DF4IAH/HFT-Core-Module/CAD/Eagle/HFT-Core-Module_1V0_BOM.txt

Stückliste exportiert aus /Users/espero/nfs_ds_nfs/git/HFT-Core-Module__HW_1V0/CAD/Eagle/HFT-Core-Module_1V0.sch am 10.08.18 23:08

Qty Value                                             Device                             Package                            Parts                                                                                                                                                                                                                                                                                                                                                                                                                                                                                                                                                                                                      Description                                                 
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
84  47R                                               R-EU_R0603                         R0603                              R0241, R0242, R0243, R0251, R0252, R0253, R0254, R0261, R0262, R0263, R0269, R0271, R0272, R0273, R0274, R0275, R0276, R0277, R0281, R0282, R0283, R0284, R0285, R0286, R0287, R0288, R0289, R0290, R0291, R0292, R0293, R0294, R0295, R0296, R0642, R0713, R0714, R0723, R0724, R0731, R0732, R0735, R0736, R0743, R0744, R0802, R0803, R0831, R1021, R1041, R1051, R1061, R1106, R1107, R1108, R1109, R1114, R2310, R2311, R2312, R2313, R2314, R2315, R2316, R2317, R2318, R2320, R2321, R2322, R2323, R2324, R2325, R2326, R2327, R2328, R2330, R2331, R2332, R2333, R2334, R2335, R2336, R2337, R2338 RESISTOR, European symbol                                   
7   47pF                                              C-EUC0603                          C0603                              C0844, C0846, C0851, C0852, C0873, C0875, C1113                                                                                                                                                                                                                                                                                                                                                                                                                                                                                                                                                            CAPACITOR, European symbol                                  
3   47uF                                              C-EUC0805                          C0805                              C1406, C1602, C1606                                                                                                                                                                                                                                                                                                                                                                                                                                                                                                                                                                                        CAPACITOR, European symbol                                  
1   5.2kR                                             R-EU_R0603                         R0603                              R1202                                                                                                                                                                                                                                                                                                                                                                                                                                                                                                                                                                                                      RESISTOR, European symbol                                   
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
