DF4IAH/HFT-Core-Module/CAD/Eagle/Extensions/Manufacturing/Pictures/HFT-ArduinoShield-Module_1V0__BottomCopper.png

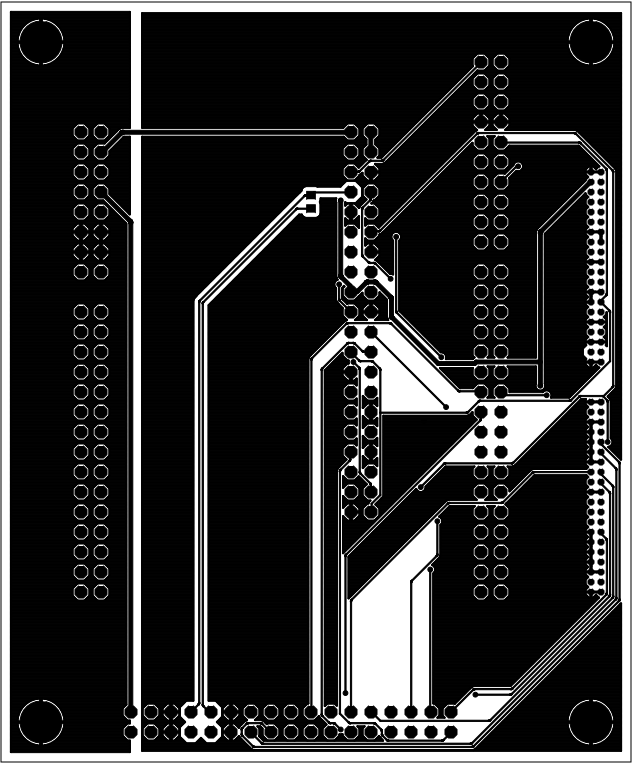
CAD/Eagle/Extensions/Manufacturing/Pictures/HFT-ArduinoShield-Module_1V0__BottomCopper.png
