DF4IAH/HFT-Core-Module/CAD/Eagle/Extensions/Manufacturing/Pictures/HFT-ArduinoShield-Module_1V0__Top.png

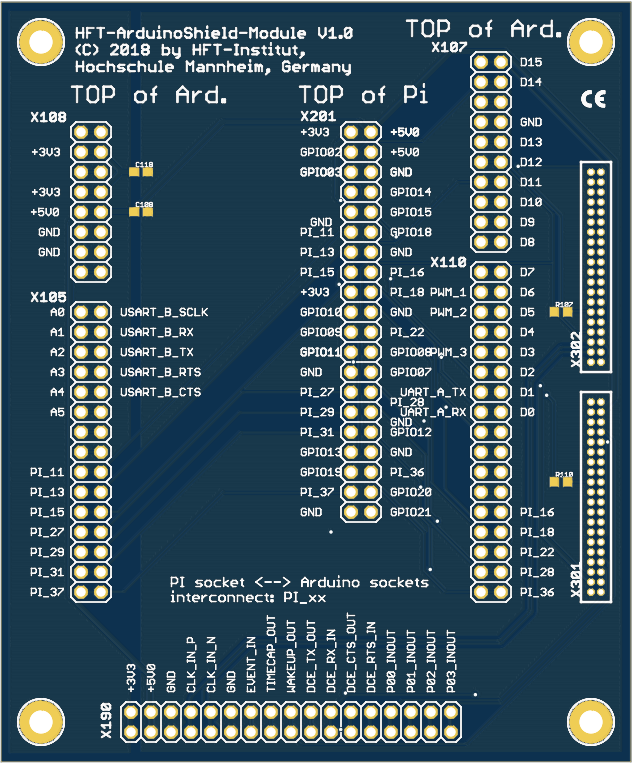
CAD/Eagle/Extensions/Manufacturing/Pictures/HFT-ArduinoShield-Module_1V0__Top.png
