DF4IAH/HFT-Core-Module/CAD/Eagle/Extensions/Manufacturing/Pictures/HFT-ArduinoShield-Module_1V0__TopSilkscreen.png

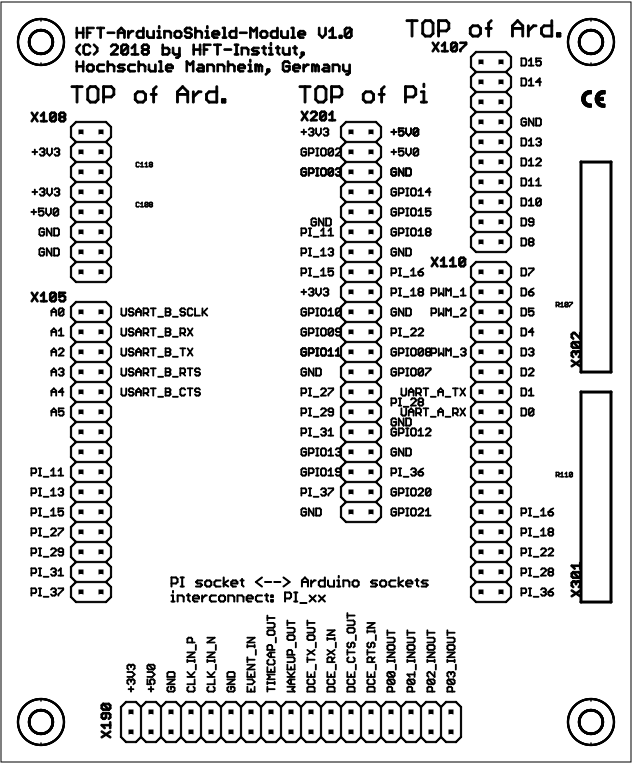
CAD/Eagle/Extensions/Manufacturing/Pictures/HFT-ArduinoShield-Module_1V0__TopSilkscreen.png
