DF4IAH/HFT-Core-Module/CAD/Eagle/Extensions/Manufacturing/Pictures/HFT-ArduinoShield-Module_1V0__TopSoldermask.png

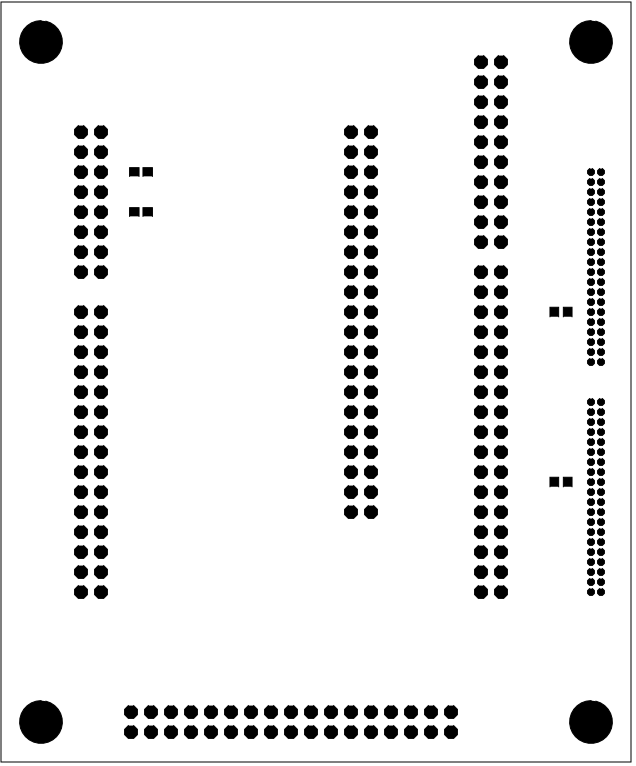
CAD/Eagle/Extensions/Manufacturing/Pictures/HFT-ArduinoShield-Module_1V0__TopSoldermask.png
