DF4IAH/HFT-Core-Module/CAD/Eagle/Manufacturing/Pictures/HFT-Core-Module_1V0__Bottom.png

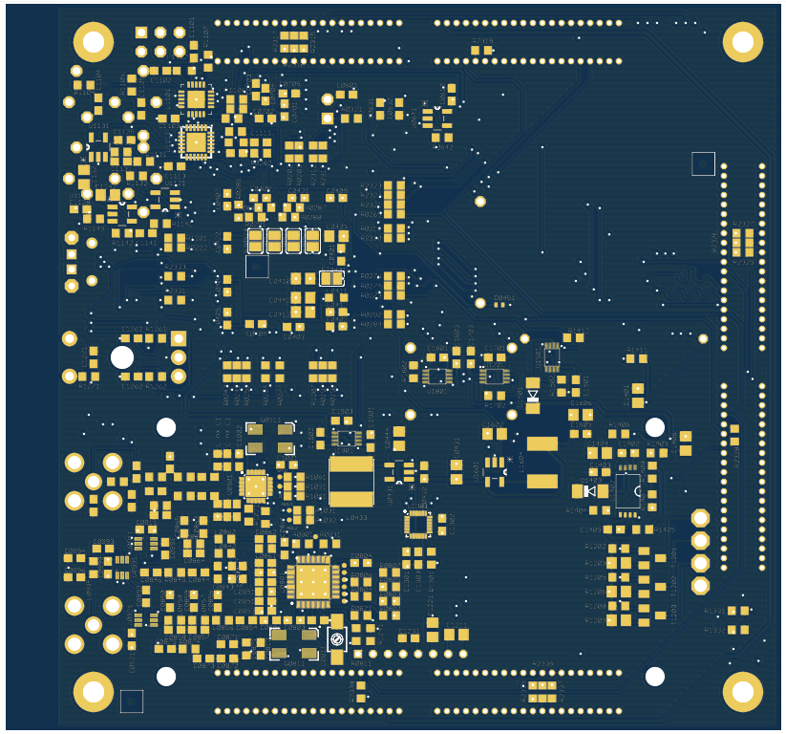
CAD/Eagle/Manufacturing/Pictures/HFT-Core-Module_1V0__Bottom.png
