DF4IAH/HFT-Core-Module/Docs/09_Results/Pictures/1V0_4-Layers_Dirty-PCB/PCB-package_1V0__IMG_2087.JPG

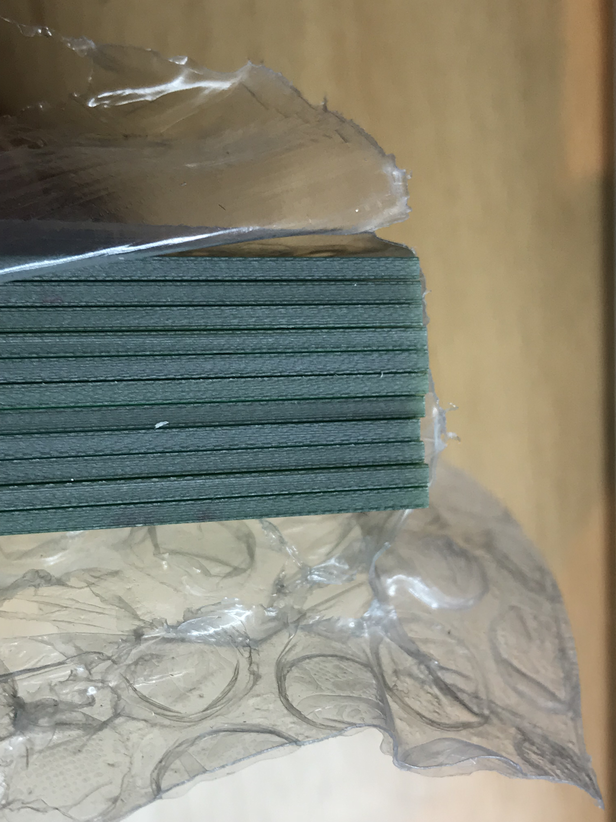
Docs/09_Results/Pictures/1V0_4-Layers_Dirty-PCB/PCB-package_1V0__IMG_2087.JPG
