DF4IAH/HFT-Core-Module/Docs/09_Results/Pictures/1V1_6-Layers_Beta-Layout/1_Preview_TOP.png

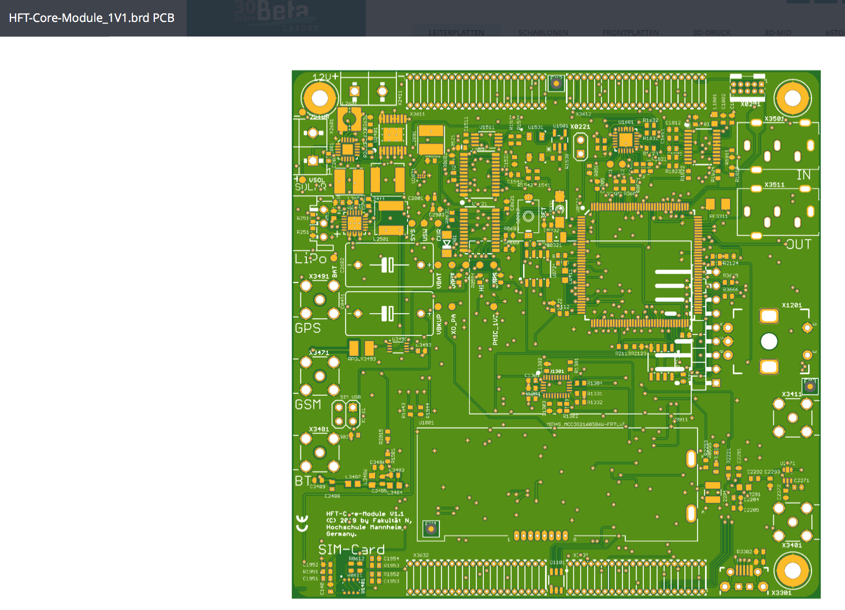
Docs/09_Results/Pictures/1V1_6-Layers_Beta-Layout/1_Preview_TOP.png
