DF4IAH/HFT-Core-Module/Docs/09_Results/Pictures/1V1_6-Layers_Beta-Layout/6_FITS-or-NOT.png

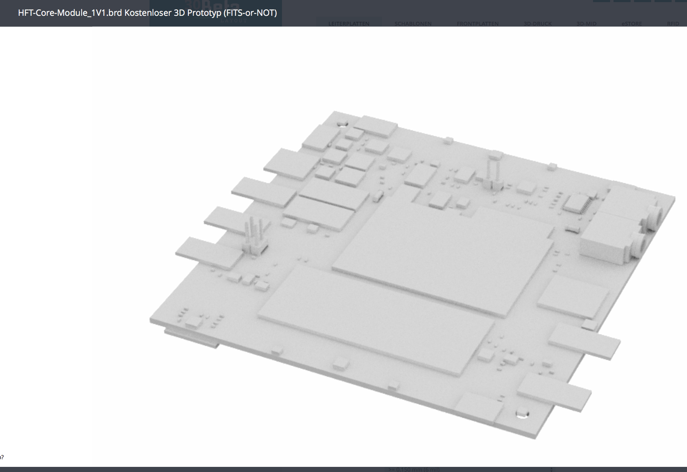
Docs/09_Results/Pictures/1V1_6-Layers_Beta-Layout/6_FITS-or-NOT.png
