DF4IAH/HFT-Core-Module/SW/HFT-Core-Module_TrueSTUDIO/App/Inc/task_Controller.h

/*
 * task_Controller.h
 *
 *  Created on: 11.09.2018
 *      Author: DF4IAH
 */

#ifndef TASK_CONTROLLER_H_
#define TASK_CONTROLLER_H_

#include "stm32l4xx_hal.h"
#include "main.h"


#define CONTROLLER_MSG_Q_LEN                                  8


typedef enum ControllerMsgDestinations_ENUM {

  Destinations__Unspec                                        = 0,
  Destinations__Controller,
  Destinations__Main_Default,

  Destinations__Osc_TCXO,
  Destinations__Osc_Si5338,

  Destinations__Network_USBtoHost,
  Destinations__Network_USBfromHost,

  Destinations__Actor_LCD,

  Destinations__Sensor_Baro,
  Destinations__Sensor_Hygro,
  Destinations__Sensor_Gyro,

  Destinations__Radio_AX5243,
  Destinations__Radio_SX1276,

  Destinations__Audio_ADC,
  Destinations__Audio_DAC,

} ControllerMsgDestinations_t;


typedef struct ControllerMods {

  uint8_t                           rtos_Default;
  uint8_t                           network_USBtoHost;
  uint8_t                           network_USBfromHost;
  uint8_t                           osc_TCXO;
  uint8_t                           osc_Si5338;
  uint8_t                           actor_LCD;
  uint8_t                           sensor_Baro;
  uint8_t                           sensor_Hygro;
  uint8_t                           sensor_Gyro;
  uint8_t                           radio_AX5243;
  uint8_t                           radio_SX1276;
  uint8_t                           audio_ADC;
  uint8_t                           audio_DAC;

} ControllerMods_t;


typedef enum ControllerMsgControllerCmds_ENUM {

  MsgController__InitDo                                       = 0x01U,
  MsgController__InitDone,

  MsgController__DeInitDo                                     = 0x05U,

//MsgController__SetVar01                                     = 0x41U,

//MsgController__GetVar01                                     = 0x81U,

  MsgController__CallFunc01_CyclicTimerEvent                  = 0xc1U,
  MsgController__CallFunc02_CyclicTimerStart,
  MsgController__CallFunc03_CyclicTimerStop,

} ControllerMsgControllerCmds_t;


typedef struct ControllerMsg2Proc {

  uint32_t                            rawAry[CONTROLLER_MSG_Q_LEN];
  uint8_t                             rawLen;

  ControllerMsgDestinations_t         msgSrc;
  ControllerMsgDestinations_t         msgDst;                                                         // Not in use yet
  ControllerMsgControllerCmds_t       msgCmd;
  uint8_t                             msgLen;

  uint8_t                             bRemain;

  uint8_t                             optLen;
  uint8_t                             optAry[CONTROLLER_MSG_Q_LEN << 2];

} ControllerMsg2Proc_t;



uint32_t controllerCalcMsgHdr(ControllerMsgDestinations_t dst, ControllerMsgDestinations_t src, uint8_t lengthBytes, uint8_t cmd);

uint32_t controllerMsgPushToInQueue(uint8_t msgLen, uint32_t* msgAry, uint32_t waitMs);
void controllerMsgPushToOutQueue(uint8_t msgLen, uint32_t* msgAry, uint32_t waitMs);
uint32_t controllerMsgPullFromOutQueue(uint32_t* msgAry, ControllerMsgDestinations_t dst, uint32_t waitMs);

void controllerTimerCallback(void const *argument);


/* Task */

void controllerTaskInit(void);
void controllerTaskLoop(void);

#endif /* TASK_CONTROLLER_H_ */
