DF4IAH/HFT-Core-Module/SW/HFT-Core-Module_TrueSTUDIO/App/Src/task_AX5243.c

/*
 * task_AX5243.c
 *
 *  Created on: 10.09.2018
 *      Author: DF4IAH
 */


/* Includes ------------------------------------------------------------------*/
#include <string.h>
#include <ctype.h>
#include <task_USB.h>
#include "FreeRTOS.h"
#include "cmsis_os.h"
#include "stm32l496xx.h"
//#include "stm32l4xx_hal_def.h"
//#include "stm32l4xx_hal_gpio.h"

#include "bus_spi.h"
#include "task_Controller.h"

#include "task_AX5243.h"


extern osSemaphoreId        c2Ax5243_BSemHandle;
extern osSemaphoreId        spi3_BSemHandle;
extern osSemaphoreId        usbToHost_BSemHandle;

extern EventGroupHandle_t   extiEventGroupHandle;
extern EventGroupHandle_t   spiEventGroupHandle;
extern EventGroupHandle_t   globalEventGroupHandle;

extern ENABLE_MASK_t        g_enableMsk;
extern MON_MASK_t           g_monMsk;

extern SPI_HandleTypeDef    hspi3;
extern DMA_HandleTypeDef    hdma_spi3_rx;
extern DMA_HandleTypeDef    hdma_spi3_tx;

extern uint8_t              spi3TxBuffer[SPI3_BUFFERSIZE];
extern uint8_t              spi3RxBuffer[SPI3_BUFFERSIZE];


/* BLOCK of DEFINITIONS */

//# define  AX_RUN_VCO2_APRS_TX       1U

//# define  AX_TEST_VCO1_BANDENDS     1U
//# define  AX_TEST_VCO1_FSK_TX       1U
//# define  AX_TEST_VCO1_FSK_RX       1U
//# define  AX_TEST_VCO1_POCSAG_TX    1U
//# define  AX_TEST_VCO1_POCSAG_RX    1U

//# define  AX_TEST_VCO2_BANDENDS     1U
//# define  AX_TEST_VCO2_ANALOG_FM_TX 1U
//# define  AX_TEST_VCO2_ANALOG_FM_RX 1U
//# define  AX_TEST_VCO2_PR1200_TX    1U
//# define  AX_TEST_VCO2_PR1200_RX    1U


#if defined(AX_TEST_VCO1_BANDENDS) | defined(AX_TEST_VCO1_FSK_TX)   | defined(AX_TEST_VCO1_FSK_RX)      | defined(AX_TEST_VCO1_FSK_RX)    | defined(AX_TEST_VCO1_POCSAG_RX) | \
  defined(AX_TEST_VCO2_BANDENDS) | defined(AX_TEST_VCO2_ANALOG_FM_TX) | defined(AX_TEST_VCO2_ANALOG_FM_RX)  | defined(AX_TEST_VCO2_PR1200_TX) | defined(AX_TEST_VCO2_PR1200_RX)
# ifndef AX_TEST
# define AX_TEST 1U
# endif
#endif


static const uint16_t       c_ax_pwr_ary[C_AX_PRW_LENGTH]     = {
  // -10.4  (< -20dBm)
  0x0000UL,

  // -10.2  (-20dBm)
  0x000aUL,

  // -10.0 .. - 9.1
    170,    173,    175,    178,    180,    182,    184,    186,    188,    189,

  // - 9.0 .. - 8.1
    191,    193,    194,    196,    198,    199,    201,    203,    205,    207,

  // - 8.0 .. - 7.1
    209,    211,    214,    216,    219,    221,    224,    227,    230,    233,

  // - 7.0 .. - 6.1
    236,    239,    243,    246,    250,    253,    257,    260,    264,    267,

  // - 6.0 .. - 5.1
    271,    275,    278,    282,    285,    289,    292,    296,    299,    303,

  // - 5.0 .. - 4.1
    306,    309,    313,    317,    320,    324,    327,    331,    335,    338,

  // - 4.0 .. - 3.1
    342,    346,    350,    354,    358,    362,    366,    370,    374,    379,

  // - 3.0 .. - 2.1
    383,    387,    392,    397,    401,    406,    411,    416,    421,    426,

  // - 2.0 .. - 1.1
    431,    436,    441,    447,    452,    457,    462,    467,    471,    476,

  // - 1.0 .. - 0.1
    480,    484,    488,    492,    495,    499,    502,    506,    510,    514,

  //   0.0 .. + 0.9
    519,    524,    529,    535,    540,    547,    553,    559,    566,    573,

  // + 1.0 .. + 1.9
    580,    587,    594,    602,    609,    616,    624,    632,    640,    648,

  // + 2.0 .. + 2.1
    656,    664,    673,    681,    690,    699,    708,    718,    727,    737,

  // + 3.0 .. + 3.9
    747,    757,    768,    778,    789,    800,    812,    824,    836,    849,

  // + 4.0 .. + 4.9
    862,    876,    889,    903,    917,    930,    942,    954,    965,    974,

  // + 5.0 .. + 5.9
    982,    988,    993,    997,   1001,   1004,   1008,   1012,   1016,   1022,

  // + 6.0 .. + 6.9
   1030,   1039,   1051,   1064,   1078,   1095,   1112,   1131,   1151,   1171,

  // + 7.0 .. + 7.9
   1193,   1215,   1238,   1261,   1284,   1307,   1329,   1350,   1369,   1388,

  // + 8.0 .. + 8.9
   1404,   1419,   1431,   1443,   1454,   1466,   1477,   1489,   1503,   1518,

  // + 9.0 .. + 9.9
   1536,   1556,   1579,   1604,   1630,   1657,   1685,   1712,   1740,   1766,

  // +10.0 .. +10.9
   1792,   1816,   1839,   1861,   1884,   1907,   1931,   1956,   1984,   2014,

  // +11.0 .. +11.9
   2048,   2085,   2126,   2169,   2215,   2263,   2313,   2363,   2414,   2465,

  // +12.0 .. +12.9
   2516,   2566,   2616,   2666,   2717,   2770,   2824,   2881,   2941,   3004,

  // +13.0 .. +13.9
   3072,   3144,   3220,   3298,   3378,   3459,   3540,   3619,   3696,   3770,

  // +14.0 .. +14.9
   3840,   3905,   3963,   4015,   4058,   4093,   4095,   4095,   4095,   4095,

  // +15.0
   4095
};

#if 0
static const uint8_t        c_ax_pocsag_activation_code[][3]  = {
  { 0, 7, 0x32},
  { 0, 7, 0x22},
  { 0, 7, 0x35},
  { 0, 7, 0x33},
  { 0, 7, 0x33},
  { 0, 7, 0x34},
  { 0, 7, 0x34},
  { 0, 7, 0x34}
};
static const uint8_t        c_ax_pocsag_activation_code_len = sizeof(c_ax_pocsag_activation_code) / 3;
#endif

static uint8_t              s_ax5243_enable;                                                          // FLASH
static uint32_t             s_ax5243StartTime;
static uint8_t              s_ax_version;
static uint8_t              s_ax_aprs_enable;                                                         // FLASH
static uint8_t              s_ax_pocsag_enable;                                                       // FLASH
//static uint8_t            s_ax_pocsag_beacon_secs;                                                  // FLASH
//static AX_SET_TX_RX_MODE_t  s_ax_set_tx_rx_mode;
static AX_SET_MON_MODE_t    s_ax_set_mon_mode;                                                        // FLASH
//static struct spi_device  s_ax_spi_device_conf;
//static  uint8_t           s_ax_spi_packet_buffer[C_SPI_AX_BUFFER_LENGTH];
//static  uint8_t           s_ax_spi_rx_buffer[C_SPI_AX_BUFFER_LENGTH];
//static  uint16_t          s_ax_spi_rx_buffer_idx;
//static  uint8_t           s_ax_spi_rx_fifo_doService;
static  uint32_t            s_ax_spi_freq_chan[2];
static  uint8_t             s_ax_spi_range_chan[2];
//static  uint8_t           s_ax_spi_vcoi_chan[2];
//static  int8_t            s_ax_spi_rx_bgnd_rssi;
static  AX_RX_FIFO_MEAS_t   s_ax_rx_fifo_meas;

//static uint8_t            s_ax_pocsag_chime_enable;
static uint32_t             s_ax_pocsag_individual_ric;
//static uint8_t            s_ax_pocsag_news_idx;



/* Forward declarations */
static uint16_t spi_ax_pocsag_skyper_RubricString_Decode(char* outBuf, uint16_t outBufSize, const char* pocsagSkyperRubricMsg, uint16_t pocsagSkyperRubricMsgLen);
static uint16_t spi_ax_pocsag_skyper_NewsString_Decode(char* outBuf, uint16_t outBufSize, const char* pocsagSkyperNewsMsg, uint16_t pocsagSkyperNewsMsgLen);
static uint8_t spiDetectAX5243(void);

#ifdef AX_TEST
static void spi_test_start_testBox(void);
static void spi_ax_test_PR1200_Rx(void);
#endif


static uint8_t getCurrent_POCSAG_TimeSlot(void)
{
  /* Get up-to-date global data */
  const uint64_t l_seconds10 = getRunTimeCounterValue() / 100ULL;

  /* Each TimeSlot takes 6.4 secs */
  return (uint8_t) ((l_seconds10 >> 6) & 0x0f);
}

static void spi_ax_FIFO_CLEAR(void)
{
  /* FIFO do a CLEAR of data and flags */
  const uint8_t txMsg[2] = { 0x28U | C_AX_REG_WR,                                                     // WR address 0x28: FIFOCMD - AX_FIFO_CMD_CLEAR_FIFO_DATA_AND_FLAGS
      0x03U
  };
  spiProcessSpi3MsgTemplate(SPI3_AX, sizeof(txMsg), txMsg);
}

static void spi_ax_FIFO_COMMIT(void)
{
  /* FIFO do a COMMIT */
  const uint8_t txMsg[2] = { 0x28U | C_AX_REG_WR,                                                     // WR address 0x28: FIFOCMD - AX_FIFO_CMD_COMMIT
      0x04U
  };
  spiProcessSpi3MsgTemplate(SPI3_AX, sizeof(txMsg), txMsg);
}


#if 0

/* ISR routines */

/* PORTC Pin3 - AX5243 IRQ */
ISR(PORTC_INT0_vect, ISR_BLOCK)
{
  uint8_t processed = 0U;

  /* IRQREQUEST: check which request is on */
  spi_ax_transport(0U, "< 0c R2 >");                                                                  // RD address 0x0C: IRQREQUEST
  uint16_t ax_spi_irq_request = (uint16_t)g_ax_spi_packet_buffer[0] << 8 | g_ax_spi_packet_buffer[1];

  /* Reason(s) for interrupt */

  /* IRQRQFIFONOTEMPTY */
  if (ax_spi_irq_request & _BV(0)) {
    uint8_t fifoRssiCmd[2] = { 0x32 };                                                                // Own variant of RSSI FIFO message

    /* Get RSSI */
    spi_ax_transport(0U, "< 40 R1 >");                                                                // RD Address 0x40: RSSI
    fifoRssiCmd[1] = g_ax_spi_packet_buffer[0];

    /* Get local adjusted copies */
    int16_t l_ax_spi_rx_rssi    = (int8_t) (fifoRssiCmd[1]);
    int16_t l_ax_spi_rx_bgnd_rssi = g_ax_spi_rx_bgnd_rssi;

    /* 64 dB offset correction */
    l_ax_spi_rx_rssi    -= 64;
    l_ax_spi_rx_bgnd_rssi -= 64;

    /* Decrease background RSSI each time to avoid blocking */
    if (-170 < l_ax_spi_rx_bgnd_rssi) {
      --g_ax_spi_rx_bgnd_rssi;
    }

    /* Abort packet when signal strength indicator falls near background noise and at least some WORDS were detected */
    if ((g_ax_spi_rx_buffer_idx >= 0x10) && (l_ax_spi_rx_rssi < (l_ax_spi_rx_bgnd_rssi + 12))) {
      /* FRMMODE abort frame */
      spi_ax_transport(0U, "< 92 07 >");                                                              // WR address 0x12: FRAMING - CRCMODE: none, FRMMODE: Raw, Pattern Match 0x06, FABORT
    }

    /* Concatenate FIFO message to local buffer */
    isr_spi_ax_fifo_readMessage();

    /* Concatenate RSSI to local buffer */
    memcpy(g_ax_spi_rx_buffer + g_ax_spi_rx_buffer_idx, fifoRssiCmd, 2);
    g_ax_spi_rx_buffer_idx += 2;

    /* Inform front-end to process the data */
    g_ax_spi_rx_fifo_doService = 1U;
    processed = 1U;
  }

  /* IRQRFIFOERROR */
  if (ax_spi_irq_request & _BV(4)) {
    /* FIFOCMD / FIFOSTAT */
    spi_ax_FIFO_CLEAR();

    processed = 1U;
  }

  /* IRQRQPLLUNLOCK */
  if (ax_spi_irq_request & _BV(5)) {
    processed = 1U;
  }

  /* RADIO EVENT = REVMDONE */
  if (ax_spi_irq_request & _BV(6)) {
    const uint8_t fifoDoneCmd = 0x01;
    memcpy(g_ax_spi_rx_buffer + g_ax_spi_rx_buffer_idx, &fifoDoneCmd, 1);
    g_ax_spi_rx_buffer_idx++;

    /* Inform front-end to process the data */
    g_ax_spi_rx_fifo_doService = 1U;
    processed = 1U;
  }

  if (!processed) {
    /* unknown request */
  }
}

void spi_ax_ISR_setFlags(uint8_t flags)
{
  if (!flags) {
    irqflags_t flags = cpu_irq_save();

    /* Disable AX5243 interrupts */
    {
      /* FIFOCMD / FIFOSTAT */
      spi_ax_FIFO_CLEAR();

      /* IRQMASK: set to none */
      spi_ax_transport(0U, "< 86 00 00 >");                                                           // WR address 0x06: IRQMASK - clear all flags
    }

    /* Turn off MCU PORTC interrupts */
    PORTC_INTCTRL = PORT_INT1LVL_OFF_gc | PORT_INT0LVL_OFF_gc;

    cpu_irq_restore(flags);

  } else {
    /* PORTC Pin3 --> INT0 */
    irqflags_t flags = cpu_irq_save();

    /* PORTC Pin3 INPUT */
    ioport_set_pin_dir(AX_IRQ_PIN, IOPORT_DIR_INPUT);

    /* PORTC Pin3 PULLHIGH, Level: low active */
    ioport_set_pin_mode(AX_IRQ_PIN, IOPORT_MODE_PULLUP | IOPORT_MODE_INVERT_PIN);

    /* Interrupt priority levels for INT1 and INT0 = Low */
    PORTC_INTCTRL = PORT_INT1LVL_OFF_gc | PORT_INT0LVL_LO_gc;

    /* Map PORTC Pin3 --> INT0 */
    PORTC_INT0MASK = _BV(3);
    PORTC_INT1MASK = 0;

    /* Enable AX5243 interrupts */
    {
      /* FIFOCMD / FIFOSTAT */
      spi_ax_FIFO_CLEAR();

      /* PINFUNCIRQ */
      spi_ax_transport(0U, "< a4 43 >");                                                              // WR address 0x24: PINFUNCIRQ - set to IRQ source, no PULLUP = !0x80, inverse = 0x40

      /* RADIOEVENTMASK */
      spi_ax_transport(0U, "< 88 00 01 >");                                                           // WR address 0x08: RADIOEVENTMASK - set to not REVMRXPARAMSETCHG !0x08, not REVMRADIOSTATECHG !0x04, REVMDONE 0x01

      /* IRQMASK */
      spi_ax_transport(0U, "< 86 00 51 >");                                                           // WR address 0x06: IRQMASK - set to Bit06:IRQMRADIOCTRL 0x040, !Bit05:IRQRQPLLUNLOCK !0x020, Bit04:IRQMFIFOERROR 0x010, Bit0:IRQMFIFONOTEMPTY 0x001
    }

    /* Clear any pending INT1 / INT0 interrupts */
    PORTC_INTFLAGS = 0b00000011;

    /* Activation of all interrupts, again */
    cpu_irq_restore(flags);
  }
}

void isr_spi_ax_fifo_readMessage(void)
{
  /* Read the length of the message within the FIFO */
  spi_ax_transport(0U, "< 2a R2 >");                           // RD address 0x2A: FIFOCOUNT
  uint16_t msgLen = (uint16_t)g_ax_spi_packet_buffer[0] << 8 | g_ax_spi_packet_buffer[1];
  if ((g_ax_spi_rx_buffer_idx + msgLen) > 256) {
    msgLen = 256 - g_ax_spi_rx_buffer_idx;
  }

  /* Fetch the AX5243 FIFO content */
  uint8_t fifoDataAddr = 0x29;
  spi_select_device(&SPI_AX, &g_ax_spi_device_conf);
  spi_write_packet(&SPI_AX, &fifoDataAddr, 1);
  spi_read_packet(&SPI_AX, g_ax_spi_rx_buffer + g_ax_spi_rx_buffer_idx, msgLen);
  spi_deselect_device(&SPI_AX, &g_ax_spi_device_conf);

  g_ax_spi_rx_buffer_idx += msgLen;
}
#endif

#if 0
static uint8_t strGetHex(const char* str)
{
  unsigned int ret = 0;

  sscanf(str, "%02x", &ret);
  return (uint8_t)ret;
}

static uint8_t strGetDec(const char* str, int* o_val)
{
  return (uint8_t) sscanf(str, "%d", o_val);
}
#endif


#ifdef WHEN_NEEDED
static AX_POCSAG_CW2_t ax_pocsag_analyze_msg_tgtFunc_get(const char* msg, uint16_t msgLen)
{
  if (!msg || !msgLen) {
    return AX_POCSAG_CW2_MODE1_TONE;
  }

  for (uint16_t idx = 0; idx < msgLen; idx++) {
    char c = *(msg + idx);

    if (('0' <= c) && (c <= '9')) {
      continue;
    }

    if ((c == ' ') || (c == '-') || (toupper(c) == 'U') || (c == '[') || (c == ']') || (c == '(') || (c == ')')) {
      continue;
    }

    return AX_POCSAG_CW2_MODE3_ALPHANUM;
  }

  return AX_POCSAG_CW2_MODE0_NUMERIC;
}
#endif

static uint8_t spi_ax_pocsag_calc_evenParity(uint32_t par)
{
  par ^= par >> 0x01;
  par ^= par >> 0x02;
  par ^= par >> 0x04;
  par ^= par >> 0x08;
  par ^= par >> 0x10;
  par &= 1;

  return (uint8_t) par;
}

static uint32_t spi_ax_pocsag_calc_checkAndParity(uint32_t codeword_in)
{
  const uint32_t inPoly   = 0xfffff800UL & codeword_in;
  const uint32_t genPoly  = 0x769UL;                                                                  // Generating polynomial   x10 + x9 + x8 + x6 + x5 + x3 + 1
  uint32_t cw_calc        = inPoly;

  // Calculate the BCH check
  for (uint8_t idx = 31; idx >= 11; idx--) {
    if (cw_calc  & (1UL <<  idx)) {
      volatile uint32_t genPolyShifted = genPoly << (idx - 10);
      cw_calc ^= genPolyShifted;
      (void)genPolyShifted;
    }
  }
  cw_calc &= 0x000007feUL;

  /* Data with BCH check */
  cw_calc |= inPoly;

  /* Calculate for Even Parity */
  uint8_t par = spi_ax_pocsag_calc_evenParity(cw_calc);

  /* Data with 31:21 BCH and Parity */
  cw_calc |= par;

  return cw_calc;
}

static uint8_t spi_ax_pocsag_getBcd(char c)
{
  uint8_t u8;

  switch (c) {
    case 0x30:
    case 0x31:
    case 0x32:
    case 0x33:
    case 0x34:
    case 0x35:
    case 0x36:
    case 0x37:
    case 0x38:
    case 0x39:
      u8 = c - 0x30;
      break;

    case 0x23:                                                                                        // #
    case 0x2a:                                                                                        // *
      u8 = 0xa;
      break;

    case 0x55:                                                                                        // U
    case 0x75:                                                                                        // u
      u8 = 0xb;
      break;

    case 0x20:                                                                                        // ' '
      u8 = 0xc;
      break;

    case 0x2d:                                                                                        // -
      u8 = 0xd;
      break;

    case 0x5d:                                                                                        // ]
    case 0x29:                                                                                        // )
      u8 = 0xe;
      break;

    case 0x5b:                                                                                        // [
    case 0x28:                                                                                        // (
      u8 = 0xf;
      break;

    default:
      u8 = 0xc;                                                                                       // ' '
  }
  return u8;
}

static char spi_ax_pocsag_getReversedNumChar(uint8_t nibble)
{
  char c;

  switch (nibble) {
    case 0b0000:
      c = 0x30;
      break;

    case 0b1000:
      c = 0x31;
      break;

    case 0b0100:
      c = 0x32;
      break;

    case 0b1100:
      c = 0x33;
      break;

    case 0b0010:
      c = 0x34;
      break;

    case 0b1010:
      c = 0x35;
      break;

    case 0b0110:
      c = 0x36;
      break;

    case 0b1110:
      c = 0x37;
      break;

    case 0b0001:
      c = 0x38;
      break;

    case 0b1001:
      c = 0x39;
      break;

    case 0b0101:                                                                                      // #
      c = 0x23;
      break;

    case 0b1101:                                                                                      // U
      c = 0x55;
      break;

    case 0b0011:                                                                                      // ' '
      c = 0x20;
      break;

    case 0b1011:                                                                                      // -
      c = 0x2d;
      break;

    case 0b0111:                                                                                      // ]
      c = 0x5d;
      break;

    case 0b1111:                                                                                      // [
      c = 0x5b;
      break;

    default:
      c = 0x20;                                                                                       // ' '
  }
  return c;
}

static char spi_ax_pocsag_getReversedAlphaChar(uint8_t reversedIn)
{
  char c = 0;

  /* Reverse 7-bit to get ASCII */
  for (uint8_t idx = 0; idx < 7; idx++) {
    /* Take LSB */
    uint8_t bit = reversedIn & 0x01;

    /* Move bit to reversed target */
    c <<= 1;
    c  |= bit;
    reversedIn >>= 1;
  }
  return c;
}

static uint32_t spi_ax_pocsag_get20Bits(const char* tgtMsg, uint16_t tgtMsgLen, AX_POCSAG_CW2_t tgtFunc, uint16_t msgBitIdx)
{
  uint32_t msgWord = 0UL;
  uint16_t msgByteIdx;
  uint16_t msgByteIdxLast = 65535;
  uint8_t  byteBitPos;
  uint8_t  byte = 0;

  for (uint16_t bitCnt = 20; bitCnt; bitCnt--, msgBitIdx++) {
    if (tgtFunc == AX_POCSAG_CW2_MODE0_NUMERIC) {
      /* Calculate source byte and bit position of byte */
      msgByteIdx  = msgBitIdx >> 2;
      byteBitPos  = msgBitIdx & 0x3;

      /* Get the byte as NUMERIC - NUMERIC_SPACE when message exhausted */
      if (msgByteIdxLast != msgByteIdx) {
        msgByteIdxLast = msgByteIdx;
        byte = (msgByteIdx < tgtMsgLen) ?  spi_ax_pocsag_getBcd(*(tgtMsg + msgByteIdx)) : 0xc;
      }

    } else {
      /* Calculate source byte and bit position of byte */
      msgByteIdx  = msgBitIdx / 7;
      byteBitPos  = msgBitIdx % 7;

      /* Get the byte as ALPHA - NULL when message exhausted */
      if (msgByteIdxLast != msgByteIdx) {
        msgByteIdxLast = msgByteIdx;
        byte = (msgByteIdx < tgtMsgLen) ?  (uint8_t) *(tgtMsg + msgByteIdx) : 0;
      }
    }

    msgWord <<= 1;
    if (byte & (1U << byteBitPos)) {
      msgWord |= 0b1;
    }
  }
  return msgWord;
}

static char spi_ax_pocsag_getNumeric(const uint32_t* rcv20Bits, uint8_t rcv20BitsCnt, uint8_t msgNumIdx)
{
  uint8_t rcv20BitsIdx  = msgNumIdx / 5;
  uint8_t innerPos    = 4 - (msgNumIdx % 5);
  uint8_t mvCnt     = innerPos << 2;
  char numChar      = ' ';

  if (rcv20BitsIdx < rcv20BitsCnt) {
    /* Get nibble slice */
    uint8_t nibble = (*(rcv20Bits + rcv20BitsIdx) >> mvCnt) & 0x0f;
    numChar = spi_ax_pocsag_getReversedNumChar(nibble);
  }
  return numChar;
}

static char spi_ax_pocsag_getAlphanum(const uint32_t* rcv20Bits, uint8_t rcv20BitsCnt, uint8_t msgAlphaIdx)
{
  uint8_t   rcv20BitsStartWordPos = (msgAlphaIdx * 7) / 20;
  uint8_t   rcv20BitsStartBitPos  = (msgAlphaIdx * 7) - (rcv20BitsStartWordPos * 20);

  /* Check for overflow */
  if ((rcv20BitsStartBitPos > 13) && ((rcv20BitsStartWordPos + 1) >= rcv20BitsCnt)) {
    return ' ';
  }

  /* Preload with MSB 20 bits */
  uint32_t charHiPad = *(rcv20Bits + rcv20BitsStartWordPos);

  /* Decide whether word concatenation is needed */
  if (rcv20BitsStartBitPos <= 13) {
    /* No overlapping */
    charHiPad >>= (13 - rcv20BitsStartBitPos);

  } else {
    /* Complete with LSB part when overlapping */

    /* Load LSB part */
    uint32_t charLoPad = *(rcv20Bits + rcv20BitsStartWordPos + 1);

    /* Move upper part to right position */
    charHiPad <<= (rcv20BitsStartBitPos - 13);

    /* Move lower part to right position */
    charLoPad >>= (33 - rcv20BitsStartBitPos);

    /* Combine into MSB pad */
    charHiPad  |= charLoPad;
  }

  /* Get character of this 7-bit field */
  return spi_ax_pocsag_getReversedAlphaChar((uint8_t) (charHiPad & 0x0000007fUL));
}


static void spi_ax_pocsag_address_tone(uint8_t is_RIC_individual, uint32_t address, uint8_t fktBits)
{
  char isMyChar = is_RIC_individual ?  '*' : ' ';
  char isMyBeep = is_RIC_individual ?  0x07 : ' ';
  int  dbgLen;
  char dbgBuf[256];

  dbgLen = (uint8_t) sprintf(dbgBuf, "\r\n>>> TS=%1X %c Address=%8lu FktBits=0x%02x  (TONE   )%c%c%c\r\n", getCurrent_POCSAG_TimeSlot(), isMyChar, address, fktBits, isMyBeep, isMyBeep, isMyBeep);
  usbLogLen(dbgBuf, dbgLen);
}

static void spi_ax_pocsag_address_numeric(uint8_t is_RIC_individual, uint32_t address, uint8_t fktBits, uint32_t* dataAry, uint8_t dataCnt)
{
  char isMyChar = is_RIC_individual ?  '*' : ' ';
  char isMyBeep = is_RIC_individual ?  0x07 : ' ';
  uint8_t digitIdx = 0;
  int  dbgLen;
  char dbgBuf[256];

  dbgLen = (uint8_t) sprintf(dbgBuf, "\r\n>>> TS=%1X %c Address=%8lu FktBits=0x%02x  (NUMERIC):", getCurrent_POCSAG_TimeSlot(), isMyChar, address, fktBits);
  usbLogLen(dbgBuf, dbgLen);

  for (uint8_t dataCntIdx = 0; dataCntIdx < dataCnt; dataCntIdx++) {
    for (uint8_t sliceIdx = 0; sliceIdx < 5; sliceIdx++, digitIdx++) {
      dbgBuf[0] = spi_ax_pocsag_getNumeric(dataAry, dataCnt, digitIdx);
      usbLogLen(dbgBuf, 1);
    }
  }

  dbgLen = (uint8_t) sprintf(dbgBuf, "%c\r\n", isMyBeep);
  usbLogLen(dbgBuf, dbgLen);
}

static void spi_ax_pocsag_address_alphanum(uint8_t is_RIC_individual, uint32_t address, uint8_t fktBits, uint32_t* dataAry, uint8_t dataCnt, AX_POCSAG_IS_SKYPER_SPECIAL_t skyperSpecial)
{
  const char* typeStr = 0;
  char isMyChar = is_RIC_individual ?  '*' : ' ';
  char isMyBeep = is_RIC_individual ?  0x07 : ' ';
  int  dbgLen;
  char dbgBuf[256];
  char l_buf[256];

  switch (skyperSpecial) {
    case 1:
      typeStr = "RUBRIC ";
    break;

    case 2:
      typeStr = "NEWS   ";
    break;

    default:
      typeStr = "ALPHA  ";
  }

  dbgLen = (uint8_t) sprintf(dbgBuf, "\r\n>>> TS=%1X %c Address=%8lu FktBits=0x%02x  (%s):", getCurrent_POCSAG_TimeSlot(), isMyChar, address, fktBits, typeStr);
  usbLogLen(dbgBuf, dbgLen);
  dbgLen = 0;

  uint8_t alphaCnt = (dataCnt * 20) / 7;
  if (alphaCnt >= sizeof(dbgBuf)) {
    /* Buffer overflow */
    return;
  }

  /* Get text data */
  for (uint8_t alphaIdx = 0; alphaIdx < alphaCnt; alphaIdx++) {
    dbgBuf[dbgLen++] = spi_ax_pocsag_getAlphanum(dataAry, dataCnt, alphaIdx);
  }

  switch (skyperSpecial) {
    case 1:
      /* Decode Rubric content */
      dbgLen = spi_ax_pocsag_skyper_RubricString_Decode(l_buf, sizeof(l_buf), dbgBuf, dbgLen);
      usbLogLen(l_buf, dbgLen);
    break;

    case 2:
      /* Decode News content */
      dbgLen = spi_ax_pocsag_skyper_NewsString_Decode(l_buf, sizeof(l_buf), dbgBuf, dbgLen);
      usbLogLen(l_buf, dbgLen);
    break;

    default:
      usbLogLen(dbgBuf, dbgLen);
  }

  dbgLen = (uint8_t) sprintf(dbgBuf, "%c\r\n", isMyBeep);
  usbLogLen(dbgBuf, dbgLen);
}

static void spi_ax_pocsag_address_skyper_activation(uint8_t is_RIC_individual, uint32_t address, uint8_t fktBits, uint32_t* dataAry, uint8_t dataCnt)
{
  char isMyChar = is_RIC_individual ?  '*' : ' ';
  char isMyBeep = is_RIC_individual ?  0x07 : ' ';
  int  dbgLen;
  char dbgBuf[256];

  dbgLen = (uint8_t) sprintf(dbgBuf, "\r\n>>> TS=%1X %c Address=%8lu FktBits=0x%02x  (ACTIVTN):", getCurrent_POCSAG_TimeSlot(), isMyChar, address, fktBits);
  usbLogLen(dbgBuf, dbgLen);

  dbgLen = (uint8_t) sprintf(dbgBuf, " TODO! %c%c%c\r\n", isMyBeep, isMyBeep, isMyBeep);
  usbLogLen(dbgBuf, dbgLen);
}


#if 0
static uint16_t spi_ax_pocsag_skyper_RIC2ActivationString(char* outBuf, uint16_t outBufSize, uint32_t RIC)
{
  uint16_t outLen = 0;

  /* Sanity checks */
  if (!outBuf || outBufSize <= c_ax_pocsag_activation_code_len) {
    return 0;
  }

  for (uint16_t codeIdx = 0; codeIdx < c_ax_pocsag_activation_code_len; codeIdx++) {
    outBuf[outLen++] = (((RIC
              >> c_ax_pocsag_activation_code[codeIdx][AX_POCSAG_SKYPER_ACTIVATION_ARY_SHIFT])
              &  c_ax_pocsag_activation_code[codeIdx][AX_POCSAG_SKYPER_ACTIVATION_ARY_MASK])
              +  c_ax_pocsag_activation_code[codeIdx][AX_POCSAG_SKYPER_ACTIVATION_ARY_OFFSET])
              &  0x7f;                              // ASCII-7bit
  }
  outBuf[outLen] = 0;

  return outLen;
}
#endif

const char          PM_POCSAG_SKYPER_TIME[]         = "%02d%02d%02d   %02d%02d%02d";
#if 0
static uint16_t spi_ax_pocsag_skyper_TimeString(char* outBuf, uint16_t outBufSize, struct calendar_date* calDat)
{
  /* Sanity checks */
  if (!outBuf || outBufSize <= 15) {
    return 0;
  }

  /* Put calendar information into Skyper time message form */
  return (uint16_t) snprintf(outBuf, outBufSize, PM_POCSAG_SKYPER_TIME, calDat->hour, calDat->minute, calDat->second, calDat->date + 1, calDat->month + 1, calDat->year % 100);
}
#endif

#if 0
const char          PM_POCSAG_SKYPER_RUBRIC_ENC[]     = "1%c%c";
static uint16_t spi_ax_pocsag_skyper_RubricString_Encode(char* outBuf, uint16_t outBufSize, uint8_t rubricNumber, const char* rubricLabel, uint16_t rubricLabelLen)
{
  /* Sanity checks */
  if (!outBuf || outBufSize < 4) {
    return 0;
  }

  /* Put rubric label into Skyper rubric message form */
  uint16_t outLen = snprintf(outBuf, outBufSize, PM_POCSAG_SKYPER_RUBRIC_ENC, ' ' + (rubricNumber - 1), ' ' + 10);

  char* outBuf_ptr    = outBuf + outLen;
  const char* read_ptr  = rubricLabel;
  for (uint16_t idx = 0; idx < rubricLabelLen; idx++) {
    *(outBuf_ptr++) = *(read_ptr++) + 1;

    /* Target buffer runs out of space */
    if (++outLen >= (outBufSize - 1)) {
      break;
    }
  }
  *outBuf_ptr = 0;
  return outLen;
}
#endif

const char          PM_POCSAG_SKYPER_RUBRIC_DEC[]     = "Rubric=%02d, MaxEntries=%02d, Name: ";
static uint16_t spi_ax_pocsag_skyper_RubricString_Decode(char* outBuf, uint16_t outBufSize, const char* pocsagSkyperRubricMsg, uint16_t pocsagSkyperRubricMsgLen)
{
  /* Sanity checks */
  if (!outBuf || outBufSize < 8 || pocsagSkyperRubricMsgLen < 3) {
    return 0;
  }

  uint8_t rubricNumber  = (pocsagSkyperRubricMsg[1] - ' ') + 1;
  uint8_t rubricSize    = pocsagSkyperRubricMsg[2] - ' ';
  uint16_t outLen     = snprintf(outBuf, outBufSize, PM_POCSAG_SKYPER_RUBRIC_DEC, rubricNumber, rubricSize);

  char* outBuf_ptr    = outBuf + outLen;
  const char* read_ptr  = pocsagSkyperRubricMsg + 3;
  for (uint16_t idx = 3; idx < pocsagSkyperRubricMsgLen; idx++) {
    *(outBuf_ptr++) = *(read_ptr++) - 1;

    /* Target buffer runs out of space */
    if (++outLen >= (outBufSize - 1)) {
      break;
    }
  }
  *outBuf_ptr = 0;
  return outLen;
}

#if 0
const char          PM_POCSAG_SKYPER_NEWS_ENC[]       = "%c%c";
static uint16_t spi_ax_pocsag_skyper_NewsString_Encode(char* outBuf, uint16_t outBufSize, uint8_t rubricNumber, uint8_t newsNumber, const char* newsString, uint16_t newsStringLen)
{
  /* Sanity checks */
  if (!outBuf || outBufSize < 2) {
    return 0;
  }

  /* Put news into Skyper news message form */
  uint16_t outLen = snprintf(outBuf, outBufSize, PM_POCSAG_SKYPER_NEWS_ENC, ' ' + (rubricNumber - 1), ' ' + newsNumber);

  char* outBuf_ptr    = outBuf + outLen;
  const char* read_ptr  = newsString;
  for (uint16_t idx = 0; idx < newsStringLen; idx++) {
    *(outBuf_ptr++) = *(read_ptr++) + 1;

    /* Target buffer runs out of space */
    if (++outLen >= (outBufSize - 1)) {
      break;
    }
  }
  *outBuf_ptr = 0;
  return outLen;
}
#endif

const char          PM_POCSAG_SKYPER_NEWS_DEC[]       = "Rubric=%02d, News#=%02d, Text: ";
static uint16_t spi_ax_pocsag_skyper_NewsString_Decode(char* outBuf, uint16_t outBufSize, const char* pocsagSkyperNewsMsg, uint16_t pocsagSkyperNewsMsgLen)
{
  /* Sanity checks */
  if (!outBuf || outBufSize < 8 || pocsagSkyperNewsMsgLen < 2) {
    return 0;
  }

  uint8_t rubricNumber  = (pocsagSkyperNewsMsg[0] - ' ') + 1;
  uint8_t newsNumber    = pocsagSkyperNewsMsg[1] - ' ';
  uint16_t outLen     = snprintf(outBuf, outBufSize, PM_POCSAG_SKYPER_NEWS_DEC, rubricNumber, newsNumber);

  char* outBuf_ptr    = outBuf + outLen;
  const char* read_ptr  = pocsagSkyperNewsMsg + 2;
  for (uint16_t idx = 2; idx < pocsagSkyperNewsMsgLen; idx++) {
    *(outBuf_ptr++) = *(read_ptr++) - 1;

    /* Target buffer runs out of space */
    if (++outLen >= (outBufSize - 1)) {
      break;
    }
  }
  *outBuf_ptr = 0;
  return outLen;
}


static void spi_ax_pocsag_wordDecoder(AX_POCSAG_DECODER_DATA_t* l_pocsagData, uint32_t pocsagWord, uint8_t pocsagWordCnt)
{
  uint8_t tryBits = 32;

  /* Sanity check */
  if (!l_pocsagData) {
    return;
  }

  /* Preparations */
  l_pocsagData->badDecode     = 1U;                                                                   // No decoding data result
  l_pocsagData->badParity     = 1U;                                                                   // Parity check on non-modified data failed
  l_pocsagData->badCheck      = 1U;                                                                   // Check on non-modified data failed
  l_pocsagData->isAddr        = 0U;
  l_pocsagData->isData        = 0U;
  l_pocsagData->addrData      = 0UL;
  l_pocsagData->functionBits  = 0;

  /* Outer loop for one bit error corrections */
  do {
    l_pocsagData->invertedBit = tryBits;

    /* Try this pattern */
    uint32_t l_pocsagWord = pocsagWord;
    if ((0x00 <= tryBits) && (tryBits < 0x20)) {
      l_pocsagWord ^= (1UL << tryBits);
    }

    /* Inner loop for CODEWORD under test */
    do {
      /* Parity check */
      uint8_t  parCalc   = spi_ax_pocsag_calc_evenParity(l_pocsagWord & 0xfffffffe);
      uint8_t  parData   = (l_pocsagWord & 0x00000001) != 0;
      uint8_t  l_badParity = (parCalc != parData);
      if (tryBits == 0x20) {
        l_pocsagData->badParity = l_badParity;
      }
      if (l_badParity) {
        break;
      }

      /* Check calculation */
      uint32_t  chkCalc   = spi_ax_pocsag_calc_checkAndParity(l_pocsagWord);
      uint8_t    l_badCheck  = (chkCalc != l_pocsagWord);
      if (tryBits == 0x20) {
        l_pocsagData->badCheck = l_badCheck;

        if (l_badCheck && !l_badParity) {
          /* At least 2 bit errors detected - abort */
          return;
        }
      }
      if (l_badCheck) {
        break;
      }

      /* Address / Data assignment */
      l_pocsagData->badDecode = 0U;
      if (!(l_pocsagWord & 0x80000000UL)) {
        /* Address - HI-part concatenated by LO-part */
        l_pocsagData->isAddr  = 1U;
        l_pocsagData->addrData  = ((l_pocsagWord >> 10) & 0x001ffff8UL) | ((pocsagWordCnt >> 1) & 0b111);

        /* Function bits */
        l_pocsagData->functionBits = (uint8_t) ((l_pocsagWord >> 11) & 0b11);

      } else {
        /* Data */
        l_pocsagData->isData  = 1U;
        l_pocsagData->addrData  = ((l_pocsagWord >> 11) & 0x000fffffUL);
      }
      return;
    } while (0U);
  } while (tryBits--);
}

static void spi_ax_pocsag_messageDecoder(uint32_t address, uint8_t functionBits, uint32_t* dataAry, uint8_t dataCnt)
{
  uint8_t isSkyper = 1U;

  if (isSkyper) {
    uint32_t l_ax_pocsag_individual_ric = s_ax_pocsag_individual_ric;

    switch (address) {
      case AX_POCSAG_SKYPER_RIC_CLOCK:
      {
        if (functionBits == AX_POCSAG_CW2_MODE0_NUMERIC) {
          /* Time information */
          spi_ax_pocsag_address_numeric(0U, address, functionBits, dataAry, dataCnt);                 // TODO: DEBUGGING ONLY
        }
      }
      break;

      case AX_POCSAG_SKYPER_RIC_RUBRICS:
      {
        if (functionBits == AX_POCSAG_CW2_MODE3_ALPHANUM) {
          /* Store list of Rubrics */
          spi_ax_pocsag_address_alphanum(0U, address, functionBits, dataAry, dataCnt, AX_POCSAG_IS_SKYPER_SPECIAL_RUBRIC);   // TODO: DEBUGGING ONLY
        }
      }
      break;

      case AX_POCSAG_SKYPER_RIC_NEWS:
      {
        if (functionBits == AX_POCSAG_CW2_MODE3_ALPHANUM) {
          /* Store News into rubrics */
          spi_ax_pocsag_address_alphanum(0U, address, functionBits, dataAry, dataCnt, AX_POCSAG_IS_SKYPER_SPECIAL_NEWS);   // TODO: DEBUGGING ONLY
        }
      }
      break;

      case 0:
      {
        /* Drop non-valid address */
      }
      break;

      default:
      {
        uint8_t is_RIC_individual = address == l_ax_pocsag_individual_ric;
        switch (functionBits) {
          case AX_POCSAG_CW2_MODE2_ACTIVATION:
          {
            /* Check activation */
            spi_ax_pocsag_address_skyper_activation(is_RIC_individual, address, functionBits, dataAry, dataCnt);
          }
          break;

          case AX_POCSAG_CW2_MODE0_NUMERIC:
          {
            /* Numeric decoder */
            spi_ax_pocsag_address_numeric(is_RIC_individual, address, functionBits, dataAry, dataCnt);
          }
          break;

          case AX_POCSAG_CW2_MODE1_TONE:
          {
            /* Beep */
            spi_ax_pocsag_address_tone(is_RIC_individual, address, functionBits);
          }
          break;

          case AX_POCSAG_CW2_MODE3_ALPHANUM:
          {
            /* Alphanum decoder */
            spi_ax_pocsag_address_alphanum(is_RIC_individual, address, functionBits, dataAry, dataCnt, AX_POCSAG_IS_SKYPER_SPECIAL_NO);
          }
          break;
        }  // switch (functionBits)
      }
    }  // switch (address)
  }  // if (isSkyper)
}

static uint8_t spi_ax_sync2Powerdown(void)
{
  /* @see AND9347/D, page 12: Preparation 1. and 2. */
  uint8_t cntr = 0xffU;

  /* SEL line and MISO check */
  {
    const uint8_t txMsg[2] = { SPI_RD_FLAG | C_AX_REG_RD,
        0x00U
    };
    uint8_t state;

    while (--cntr) {
      spiProcessSpi3MsgTemplateLocked(SPI3_AX, sizeof(txMsg), txMsg, 1U);
      state = spi3RxBuffer[1];
      osSemaphoreRelease(spi3_BSemHandle);

      if (state > 0) {
        break;
      }

      osThreadYield();
    }

    if (!cntr) {
      /* Timeout */
      return HAL_TIMEOUT;
    }
  }

  /* Set RESET with Powerdown mode */
  {
    const uint8_t txMsg[2] = { 0x02U | C_AX_REG_WR,                                                   // WR address 0x02: PWRMODE - RESET, PWRMODE=Powerdown
        0x80U
    };
    spiProcessSpi3MsgTemplate(SPI3_AX, sizeof(txMsg), txMsg);
  }

  /* Clear RESET and go to Powerdown */
  {
    const uint8_t txMsg[2] = { 0x02U | C_AX_REG_WR,                                                   // WR address 0x02: PWRMODE - RESET, PWRMODE=Powerdown
        0x00U
    };
    spiProcessSpi3MsgTemplate(SPI3_AX, sizeof(txMsg), txMsg);
  }

  /* Ready to program register file */
  /* @see AND9347/D, page 12: Preparation 3. */
  return HAL_OK;
}

static void spi_ax_xtal_waitReady(void)
{
  const uint8_t txMsg[2] = { 0x1dU | C_AX_REG_RD,                                                     // RD Address 0x1D: XTALSTATUS
      0x00U
  };
  uint8_t state = 0U;

  /*  Wait until crystal oscillator is ready */
  do {
    spiProcessSpi3MsgTemplateLocked(SPI3_AX, sizeof(txMsg), txMsg, 1U);
    state = spi3RxBuffer[1] & 0x01U;                                                                  // Bit 0: XTALRUN
    osSemaphoreRelease(spi3_BSemHandle);

    if (state) {
      break;
    }

    /* Wait some time away */
    osDelay(5);
  } while (1);
}

static void spi_ax_setPower_dBm(float dBm)
{
  /* Range -10dBm .. +15dBm */

  uint16_t pwrReg; (void) pwrReg;
  uint8_t pwrIdx;

  if (dBm > 15.f) {
    dBm = 15.f;

  } else if (dBm < -20.f) {
    dBm = -10.2f;

  } else if (dBm < -10.f) {
    dBm = -10.1f;
  }

  pwrIdx = (uint8_t) ((dBm + 10.2f) * 10.f + 0.5f);
  pwrReg = c_ax_pwr_ary[pwrIdx];

  /* Set power register value */
  {
    const uint8_t txMsg[4] = { 0xF1U, 0x6AU,                                                          // WR Address 0x16A: TXPWRCOEFFB
        (uint8_t) (pwrReg >> 8), (uint8_t) (pwrReg  & 0xff)
    };
    spiProcessSpi3MsgTemplate(SPI3_AX, sizeof(txMsg), txMsg);
  }
}

static void spi_ax_setPwrMode(AX_SET_REGISTERS_POWERMODE_t powerState)
{
  /* XOEN and REFEN when oscillator active power modes */
  powerState &= 0x0f;
  if (powerState & 0b1100) {
    powerState |= 0x60;
  }

  /* Prepare packet */
  {
    const uint8_t txMsg[2] = { 0x02 | C_AX_REG_WR,                                                    // WR address 0x02: PWRMODE
        (uint8_t) powerState
    };
    spiProcessSpi3MsgTemplate(SPI3_AX, sizeof(txMsg), txMsg);
  }
}

static void spi_ax_setRegisters(uint8_t doReset, AX_SET_REGISTERS_MODULATION_t modulation, AX_SET_REGISTERS_VARIANT_t variant, AX_SET_REGISTERS_POWERMODE_t powerState)
{
  static AX_SET_REGISTERS_MODULATION_t s_modulation = AX_SET_REGISTERS_MODULATION_NONE;
  static AX_SET_REGISTERS_VARIANT_t    s_variant    = AX_SET_REGISTERS_VARIANT_NONE;
  static AX_SET_REGISTERS_POWERMODE_t  s_powerState = AX_SET_REGISTERS_POWERMODE_NONE;

  /* Do not access the registers when not enabled */
  if (!s_ax5243_enable) {
    return;
  }

  /* Allow to reset to unknown state */
  if (modulation == AX_SET_REGISTERS_MODULATION_INVALIDATE) {
    s_modulation = AX_SET_REGISTERS_MODULATION_NONE;
  }
  if (variant == AX_SET_REGISTERS_VARIANT_INVALIDATE) {
    s_variant = AX_SET_REGISTERS_VARIANT_NONE;
  }

  /* Sanity check */
  if (powerState == AX_SET_REGISTERS_POWERMODE_NONE) {
    return;
  }

  /* Entering DEEPSLEEP - all register contents are lost */
  if (powerState == AX_SET_REGISTERS_POWERMODE_DEEPSLEEP) {
    //spi_ax_ISR_setFlags(0x00);

    s_modulation  = AX_SET_REGISTERS_MODULATION_NONE;
    s_variant   = AX_SET_REGISTERS_VARIANT_NONE;
    s_powerState  = powerState;

    spi_ax_setPwrMode(powerState);
    return;
  }

  if (doReset) {
    //spi_ax_ISR_setFlags(0x00);

    s_modulation  = AX_SET_REGISTERS_MODULATION_NONE;
    s_variant     = AX_SET_REGISTERS_VARIANT_NONE;
    s_powerState  = AX_SET_REGISTERS_POWERMODE_POWERDOWN;

    if (HAL_OK != spi_ax_sync2Powerdown()) {
      s_ax5243_enable = 0U;
      return;
    }
  }

  /* Copy when NO_CHANGE */
  {
    if ((modulation == AX_SET_REGISTERS_MODULATION_NO_CHANGE) && (s_modulation != AX_SET_REGISTERS_MODULATION_NONE)) {
      modulation = s_modulation;
    }

    if ((variant == AX_SET_REGISTERS_VARIANT_NO_CHANGE)     && (s_variant != AX_SET_REGISTERS_VARIANT_NONE)) {
      variant = s_variant;
    }
  }

  /* No change, leave */
  if ((s_modulation == modulation) && (s_variant == variant) && (s_powerState == powerState)) {
    return;
  }

  /* Register file modifications */
  if (((modulation != AX_SET_REGISTERS_MODULATION_INVALIDATE) && (s_modulation != modulation)) ||
      ((variant    != AX_SET_REGISTERS_VARIANT_INVALIDATE)    && (s_variant    != variant   ))) {

    /* Go to POWERDOWN mode for register file modifications */
    if (s_powerState != AX_SET_REGISTERS_POWERMODE_POWERDOWN) {
      //spi_ax_ISR_setFlags(0x00);
      s_powerState = AX_SET_REGISTERS_POWERMODE_POWERDOWN;
      spi_ax_setPwrMode(s_powerState);
    }

    /* Overwrite with modulation settings */
    switch (modulation) {
      case AX_SET_REGISTERS_MODULATION_FSK:
      {
        if (s_modulation != modulation) {
          s_modulation  = AX_SET_REGISTERS_MODULATION_FSK;
          s_variant     = AX_SET_REGISTERS_VARIANT_NONE;
        }

        /* Overwrite with variant settings */
        if (s_variant != variant) {
          s_variant = variant;

          switch (variant) {
            case AX_SET_REGISTERS_VARIANT_TX:
            {
              spi_ax_initRegisters_FSK();
              spi_ax_initRegisters_FSK_Tx();
            }
            break;

            case AX_SET_REGISTERS_VARIANT_RX:
            {
              spi_ax_initRegisters_FSK();
              spi_ax_initRegisters_FSK_Rx();
            }
            break;

            default:
            {
              /* Nothing to be set */
            }
          }  // switch (variant)
        }  // if (s_variant != variant)
      }  // case AX_SET_REGISTERS_MODULATION_FSK
      break;

      case AX_SET_REGISTERS_MODULATION_PR1200:
      {
        if (s_modulation != modulation) {
          s_modulation  = AX_SET_REGISTERS_MODULATION_PR1200;
          s_variant     = AX_SET_REGISTERS_VARIANT_NONE;
        }

        /* Overwrite with variant settings */
        if (s_variant != variant) {
          s_variant = variant;

          switch (variant) {
            case AX_SET_REGISTERS_VARIANT_TX:
            {
              spi_ax_initRegisters_PR1200();
              spi_ax_initRegisters_PR1200_Tx();
            }
            break;

            case AX_SET_REGISTERS_VARIANT_RX_WOR:
            {
              spi_ax_initRegisters_PR1200();
              spi_ax_initRegisters_PR1200_Rx();
              spi_ax_initRegisters_PR1200_Rx_WoR();
              //spi_ax_ISR_setFlags(0x01);
            }
            break;

            case AX_SET_REGISTERS_VARIANT_RX_CONT:
            case AX_SET_REGISTERS_VARIANT_RX:
            {
              spi_ax_initRegisters_PR1200();
              spi_ax_initRegisters_PR1200_Rx();
              spi_ax_initRegisters_PR1200_Rx_cont();
              //spi_ax_ISR_setFlags(0x01);
            }
            break;

            case AX_SET_REGISTERS_VARIANT_RX_CONT_SINGLEPARAMSET:
            {
              spi_ax_initRegisters_PR1200();
              spi_ax_initRegisters_PR1200_Rx();
              spi_ax_initRegisters_PR1200_Rx_cont();
              spi_ax_initRegisters_PR1200_Rx_cont_SingleParamSet();
              //spi_ax_ISR_setFlags(0x01);
            }
            break;

            default:
            {
              /* Nothing to be set */
            }
          }  // switch (variant)
        }  // if (s_variant != variant)
      }  // case AX_SET_REGISTERS_MODULATION_PR1200
      break;

      case AX_SET_REGISTERS_MODULATION_POCSAG:
      {
        if (s_modulation != modulation) {
          s_modulation  = AX_SET_REGISTERS_MODULATION_POCSAG;
          s_variant   = AX_SET_REGISTERS_VARIANT_NONE;
        }

        /* Overwrite with variant settings */
        if (s_variant != variant) {
          s_variant = variant;

          switch (variant) {
            case AX_SET_REGISTERS_VARIANT_TX:
            {
              spi_ax_initRegisters_POCSAG();
              spi_ax_initRegisters_POCSAG_Tx();
            }
            break;

            case AX_SET_REGISTERS_VARIANT_RX_WOR:
            {
              spi_ax_initRegisters_POCSAG();
              spi_ax_initRegisters_POCSAG_Rx();
              spi_ax_initRegisters_POCSAG_Rx_WoR();
              //spi_ax_ISR_setFlags(0x01);
            }
            break;

            case AX_SET_REGISTERS_VARIANT_RX_CONT:
            case AX_SET_REGISTERS_VARIANT_RX:
            {
              spi_ax_initRegisters_POCSAG();
              spi_ax_initRegisters_POCSAG_Rx();
              spi_ax_initRegisters_POCSAG_Rx_cont();
              //spi_ax_ISR_setFlags(0x01);
            }
            break;

            case AX_SET_REGISTERS_VARIANT_RX_CONT_SINGLEPARAMSET:
            {
              spi_ax_initRegisters_POCSAG();
              spi_ax_initRegisters_POCSAG_Rx();
              spi_ax_initRegisters_POCSAG_Rx_cont();
              //spi_ax_initRegisters_POCSAG_Rx_cont_SingleParamSet();
              //spi_ax_ISR_setFlags(0x01);
            }
            break;

            default:
            {
              /* Nothing to be set */
            }
          }  // switch (variant)
        }  // if (s_variant != variant)
      }
      break;

      case AX_SET_REGISTERS_MODULATION_ANALOG_FM:
      {
        if (s_modulation != modulation) {
          s_modulation  = AX_SET_REGISTERS_MODULATION_ANALOG_FM;
          s_variant     = AX_SET_REGISTERS_VARIANT_NONE;
        }

        /* Overwrite with variant settings */
        if (s_variant != variant) {
          s_variant  = variant;

          switch (variant) {
            case AX_SET_REGISTERS_VARIANT_TX:
            {
              spi_ax_initRegisters_AnlogFM();
              spi_ax_initRegisters_AnlogFM_Tx();
            }
            break;

            case AX_SET_REGISTERS_VARIANT_RX:
            case AX_SET_REGISTERS_VARIANT_RX_CONT:
            case AX_SET_REGISTERS_VARIANT_RX_WOR:
            case AX_SET_REGISTERS_VARIANT_RX_CONT_SINGLEPARAMSET:
            {
              spi_ax_initRegisters_AnlogFM();
              spi_ax_initRegisters_AnlogFM_Rx();
            }
            break;

            default:
            {
              /* Nothing to be set */
            }
          }  // switch (variant)
        }  // if (s_variant != variant)
      }
      break;

      default:
      {
        /* Nothing to be set */
      }
    }  // switch (modulation)
  }


  /* Finally enter desired powerState */
  switch (powerState) {
    case AX_SET_REGISTERS_POWERMODE_WOR:
    case AX_SET_REGISTERS_POWERMODE_DEEPSLEEP:
    case AX_SET_REGISTERS_POWERMODE_POWERDOWN:
    {
      if (s_powerState != powerState) {
        s_powerState = powerState;
        spi_ax_setPwrMode(powerState);
      }
      return;
    }
    break;

    case AX_SET_REGISTERS_POWERMODE_FIFO:
    case AX_SET_REGISTERS_POWERMODE_STANDBY:
    {
      if (s_powerState != powerState) {
        s_powerState = powerState;
        spi_ax_setPwrMode(s_powerState);
        spi_ax_xtal_waitReady();                                                                      // T_xtal
      }
      return;
    }
    break;

    case AX_SET_REGISTERS_POWERMODE_SYNTHRX:
    {
      switch (s_powerState) {
        case AX_SET_REGISTERS_POWERMODE_POWERDOWN:
        {
          s_powerState  = AX_SET_REGISTERS_POWERMODE_STANDBY;
          spi_ax_setPwrMode(s_powerState);
          spi_ax_xtal_waitReady();                                                                    // T_xtal

          s_powerState = AX_SET_REGISTERS_POWERMODE_SYNTHRX;
          spi_ax_setPwrMode(s_powerState);
          osDelay(5);                                                                                 // T_synth: >40us
        }
        break;

        case AX_SET_REGISTERS_POWERMODE_STANDBY:
        {
          s_powerState = AX_SET_REGISTERS_POWERMODE_SYNTHRX;
          spi_ax_setPwrMode(s_powerState);
          osDelay(5);                                                                                 // T_synth: >40us
        }
        break;

        case AX_SET_REGISTERS_POWERMODE_SYNTHRX:
        {
          // unused
        }
        break;

        case AX_SET_REGISTERS_POWERMODE_FULLRX:
        {
          s_powerState = AX_SET_REGISTERS_POWERMODE_SYNTHRX;
          spi_ax_setPwrMode(s_powerState);
          // ?
        }
        break;

        case AX_SET_REGISTERS_POWERMODE_SYNTHTX:
        case AX_SET_REGISTERS_POWERMODE_FULLTX:
        {
          s_powerState = AX_SET_REGISTERS_POWERMODE_STANDBY;
          spi_ax_setPwrMode(s_powerState);
          // ?

          s_powerState = AX_SET_REGISTERS_POWERMODE_SYNTHRX;
          spi_ax_setPwrMode(s_powerState);
          osDelay(5);                                                                                 // T_synth: >40us
        }
        break;

        default: { }
      }  // switch (s_powerState)
    }
    break;

    case AX_SET_REGISTERS_POWERMODE_FULLRX:
    {
      switch (s_powerState) {
        case AX_SET_REGISTERS_POWERMODE_POWERDOWN:
        {
          s_powerState = AX_SET_REGISTERS_POWERMODE_STANDBY;
          spi_ax_setPwrMode(s_powerState);
          spi_ax_xtal_waitReady();                                                                    // T_xtal

          s_powerState = AX_SET_REGISTERS_POWERMODE_SYNTHRX;
          spi_ax_setPwrMode(s_powerState);
          osDelay(5);                                                                                 // T_synth: >40us

          s_powerState = AX_SET_REGISTERS_POWERMODE_FULLRX;
          spi_ax_setPwrMode(s_powerState);
          osDelay(5);                                                                                 // T_rx_rssi
        }
        break;

        case AX_SET_REGISTERS_POWERMODE_STANDBY:
        {
          s_powerState = AX_SET_REGISTERS_POWERMODE_SYNTHRX;
          spi_ax_setPwrMode(s_powerState);
          osDelay(5);                                                                                 // T_synth: >40us

          s_powerState = AX_SET_REGISTERS_POWERMODE_FULLRX;
          spi_ax_setPwrMode(s_powerState);
          osDelay(5);                                                                                 // T_rx_rssi
        }
        break;

        case AX_SET_REGISTERS_POWERMODE_SYNTHRX:
        {
          s_powerState = AX_SET_REGISTERS_POWERMODE_FULLRX;
          spi_ax_setPwrMode(s_powerState);
          osDelay(5);                                                                                 // T_rx_rssi
        }
        break;

        case AX_SET_REGISTERS_POWERMODE_FULLRX:
        {
          // unused
        }
        break;

        case AX_SET_REGISTERS_POWERMODE_SYNTHTX:
        case AX_SET_REGISTERS_POWERMODE_FULLTX:
        {
          s_powerState = AX_SET_REGISTERS_POWERMODE_STANDBY;
          spi_ax_setPwrMode(s_powerState);
          // ?

          s_powerState = AX_SET_REGISTERS_POWERMODE_SYNTHRX;
          spi_ax_setPwrMode(s_powerState);
          osDelay(5);                                                                                 // T_synth: >40us

          s_powerState = AX_SET_REGISTERS_POWERMODE_FULLRX;
          spi_ax_setPwrMode(s_powerState);
          osDelay(5);                                                                                 // T_rx_rssi
        }
        break;

        default: { }
      }  // switch (s_powerState)
    }
    break;

    case AX_SET_REGISTERS_POWERMODE_SYNTHTX:
    {
      switch (s_powerState) {
        case AX_SET_REGISTERS_POWERMODE_POWERDOWN:
        {
          s_powerState = AX_SET_REGISTERS_POWERMODE_STANDBY;
          spi_ax_setPwrMode(s_powerState);
          spi_ax_xtal_waitReady();                                                                    // T_xtal

          s_powerState = AX_SET_REGISTERS_POWERMODE_SYNTHTX;
          spi_ax_setPwrMode(s_powerState);
          osDelay(5);                                                                                 // T_synth: >40us
        }
        break;

        case AX_SET_REGISTERS_POWERMODE_STANDBY:
        {
          s_powerState = AX_SET_REGISTERS_POWERMODE_SYNTHTX;
          spi_ax_setPwrMode(s_powerState);
          osDelay(5);                                                                                 // T_synth: >40us
        }
        break;

        case AX_SET_REGISTERS_POWERMODE_SYNTHRX:
        case AX_SET_REGISTERS_POWERMODE_FULLRX:
        {
          s_powerState = AX_SET_REGISTERS_POWERMODE_STANDBY;
          spi_ax_setPwrMode(s_powerState);
          // ?

          s_powerState = AX_SET_REGISTERS_POWERMODE_SYNTHTX;
          spi_ax_setPwrMode(s_powerState);
          osDelay(5);                                                                                 // T_synth: >40us
        }
        break;

        case AX_SET_REGISTERS_POWERMODE_SYNTHTX:
        {
          // unused
        }
        break;

        case AX_SET_REGISTERS_POWERMODE_FULLTX:
        {
          s_powerState = AX_SET_REGISTERS_POWERMODE_FULLTX;
          spi_ax_setPwrMode(s_powerState);
          osDelay(5);                                                                                 // T_tx_on
        }
        break;

        default: { }
      }  // switch (s_powerState)
    }
    break;

    case AX_SET_REGISTERS_POWERMODE_FULLTX:
    {
      switch (s_powerState) {
        case AX_SET_REGISTERS_POWERMODE_POWERDOWN:
        {
          s_powerState = AX_SET_REGISTERS_POWERMODE_STANDBY;
          spi_ax_setPwrMode(s_powerState);
          spi_ax_xtal_waitReady();                                                                    // T_xtal

          s_powerState = AX_SET_REGISTERS_POWERMODE_SYNTHTX;
          spi_ax_setPwrMode(s_powerState);
          osDelay(5);                                                                                 // T_synth: >40us

          s_powerState = AX_SET_REGISTERS_POWERMODE_FULLTX;
          spi_ax_setPwrMode(s_powerState);
          osDelay(5);                                                                                 // T_tx_on
        }
        break;

        case AX_SET_REGISTERS_POWERMODE_STANDBY:
        {
          s_powerState = AX_SET_REGISTERS_POWERMODE_SYNTHTX;
          spi_ax_setPwrMode(s_powerState);
          osDelay(5);                                                                                 // T_synth: >40us

          s_powerState = AX_SET_REGISTERS_POWERMODE_FULLTX;
          spi_ax_setPwrMode(s_powerState);
          osDelay(5);                                                                                 // T_tx_on
        }
        break;

        case AX_SET_REGISTERS_POWERMODE_SYNTHRX:
        case AX_SET_REGISTERS_POWERMODE_FULLRX:
        {
          s_powerState = AX_SET_REGISTERS_POWERMODE_STANDBY;
          spi_ax_setPwrMode(s_powerState);
          // ?

          s_powerState = AX_SET_REGISTERS_POWERMODE_SYNTHTX;
          spi_ax_setPwrMode(s_powerState);
          osDelay(5);                                                                                 // T_synth: >40us

          s_powerState = AX_SET_REGISTERS_POWERMODE_FULLTX;
          spi_ax_setPwrMode(s_powerState);
          osDelay(5);                                                                                 // T_tx_on
        }
        break;

        case AX_SET_REGISTERS_POWERMODE_SYNTHTX:
        {
          s_powerState = AX_SET_REGISTERS_POWERMODE_SYNTHTX;
          spi_ax_setPwrMode(s_powerState);
          // ?
        }
        break;

        case AX_SET_REGISTERS_POWERMODE_FULLTX:
        {
          // unused
        }
        break;

        default: { }
      }  // switch (s_powerState)
    }
    break;

    default: { }
  }  // switch (powerState)
}


static uint32_t spi_ax_calcFrequency_Mhz2Regs(float f_mhz)
{
  const float xtal_hz = 16E+6f;                               // XTAL = 16 MHz
  const float reg_per_mhz = (1LL << 24) * 1E+6f / xtal_hz;
  return (uint32_t) (0.5f + f_mhz * reg_per_mhz);
}

static float spi_ax_calcFrequency_Regs2MHz(uint32_t vco_regval)
{
  const float xtal_hz = 16E+6f;                               // XTAL = 16 MHz
  const float reg_per_mhz = (1LL << 24) * 1E+6f / xtal_hz;
  return vco_regval / reg_per_mhz;
}

static void spi_ax_setFrequency2Regs(uint8_t chan, uint8_t isFreqB)
{
  uint32_t f_reg;  (void) f_reg;

  if (chan > 2) {
    /* ERROR */
    return;
  }
  f_reg = s_ax_spi_freq_chan[chan];

  /* Make range value non-valid again */
  s_ax_spi_range_chan[chan] = C_SPI_AX_RANGE_NOT_SET;

  /* Write frequency */
  {
    const uint8_t txMsg[5] = {
        (isFreqB ?  0x3CU : 0x34U) | C_AX_REG_WR,
        (uint8_t) (f_reg >> 24) & 0xff,
        (uint8_t) (f_reg >> 16) & 0xff,
        (uint8_t) (f_reg >>  8) & 0xff,
        (uint8_t) (f_reg      ) & 0xff };                                                             // WR Address 0x34 or 0x3C
    spiProcessSpi3MsgTemplate(SPI3_AX, sizeof(txMsg), txMsg);
  }
}

static void spi_ax_doRanging(void)
{
  //static uint8_t  sf_ax_spi_range_chan[2] = { 0x28, 0x28 };
  static uint32_t sf_ax_spi_freq_chan[2] = { 0UL };

  if ((0x00 <= s_ax_spi_range_chan[0]) && (s_ax_spi_range_chan[0] <= 0x0f)  &&  (s_ax_spi_freq_chan[0] == s_ax_spi_freq_chan[0])  &&
      (0x00 <= s_ax_spi_range_chan[1]) && (s_ax_spi_range_chan[1] <= 0x0f)  &&  (s_ax_spi_freq_chan[1] == s_ax_spi_freq_chan[1])) {

    spi_ax_setRegisters(0U, AX_SET_REGISTERS_MODULATION_NO_CHANGE, AX_SET_REGISTERS_VARIANT_NO_CHANGE, AX_SET_REGISTERS_POWERMODE_POWERDOWN);

    /* Recall the ranging values for both frequencies FREQA and FREQB */
    for (uint8_t idx = 0; idx < 2; idx++) {
      uint8_t regAdr = idx ?  0x3b : 0x33;  (void) regAdr;                                            // WR Address 0x33: PLLRANGINGA  or  Address 0x3b: PLLRANGINGB
      uint8_t val = s_ax_spi_range_chan[idx];  (void) val;

      /* Write ranging value */
      {
        const uint8_t txMsg[2] = { regAdr | C_AX_REG_WR, val & 0x0fU };
        spiProcessSpi3MsgTemplate(SPI3_AX, sizeof(txMsg), txMsg);
      }
    }

  } else {
    /* Do automatic ranging */

    /* POWERMODE STANDBY */
    spi_ax_setRegisters(0U, AX_SET_REGISTERS_MODULATION_FSK, AX_SET_REGISTERS_VARIANT_NO_CHANGE, AX_SET_REGISTERS_POWERMODE_STANDBY);

    /* MODULATION */
    {
      const uint8_t txMsg[2] = { 0x10U | C_AX_REG_WR,                                                 // WR address 0x10: MODULATION - 08: FSK
          0x08U
      };
      spiProcessSpi3MsgTemplate(SPI3_AX, sizeof(txMsg), txMsg);
    }

    /* Default 100kHz loop BW for ranging */
    /* PLLLOOP */
    {
      const uint8_t txMsg[2] = { 0x30U | C_AX_REG_WR,                                                 // WR address 0x30: PLLLOOP - DIRECT: Bypass External Filter Pin, FLT: Internal Loop Filter x1 --> BW = 100 kHz for I_CP = 68 µA
          0x09U
      };
      spiProcessSpi3MsgTemplate(SPI3_AX, sizeof(txMsg), txMsg);
    }

    /* PLLCPI */
    {
      const uint8_t txMsg[2] = { 0x31U | C_AX_REG_WR,                                                 // WR address 0x31: PLLCPI - PLLCPI: Charge pump current in multiples of 8.5 µA --> I_CP = 68 µA
          0x08U
      };
      spiProcessSpi3MsgTemplate(SPI3_AX, sizeof(txMsg), txMsg);
    }

    /* FSKDEV */
    {
      const uint8_t txMsg[5] = { 0xf1U, 0x61U,                                                        // WR address 0x161: FSKDEV - off
          0x00U, 0x00U, 0x00U
      };
      spiProcessSpi3MsgTemplate(SPI3_AX, sizeof(txMsg), txMsg);
    }

    for (uint8_t idx = 0; idx < 2; idx++) {
      if ((0x10 <= s_ax_spi_range_chan[idx]) || (sf_ax_spi_freq_chan[idx] != s_ax_spi_freq_chan[idx]))
      {
        uint8_t regAdr = idx ?  0x3b : 0x33;                                                          // WR Address 0x33: PLLRANGINGA  or  Address 0x3b: PLLRANGINGB

        /* Switch to VCO1 or VCO2 as needed */
        (void) spi_ax_vco_select(s_ax_spi_freq_chan[idx], 1U);

        /* Command message */
        {
          const uint8_t txMsg[2] = { regAdr | C_AX_REG_WR,
              0x18U                                                                                   // Bit 4: RNGSTART, ranging start value = 8
          };
          spiProcessSpi3MsgTemplate(SPI3_AX, sizeof(txMsg), txMsg);
        }

        /* Wait until ranging has ended */
        uint8_t l_rangingRegVal = 0;
        {
          const uint8_t txMsg[2] = { regAdr | C_AX_REG_RD,
              0x00U                                                                                   // Bit 4: RNGSTATUS
          };
          uint8_t rngVal, rngState;

          do {
            spiProcessSpi3MsgTemplateLocked(SPI3_AX, sizeof(txMsg), txMsg, 1U);
            rngVal    = spi3RxBuffer[1];
            rngState  = rngVal & (1U << 4);
            osSemaphoreRelease(spi3_BSemHandle);

            if (!rngState) {
              break;
            }

            /* Wait some time */
            osDelay(5);
          } while (1);

          l_rangingRegVal = rngVal;
        }

        /* Ranging value to be stored - when error occurs store that result, also */
        //sf_ax_spi_range_chan[idx] = l_rangingRegVal;
        sf_ax_spi_freq_chan[idx]  = s_ax_spi_freq_chan[idx];

        /* When ranging has failed set default ranging value to keep VCO stable */
        if (l_rangingRegVal & (1UL << 5)) {
          /* Command message */
          const uint8_t txMsg[2] = { regAdr | C_AX_REG_WR, 0x08U };                                   // Ranging default value = 8
          spiProcessSpi3MsgTemplate(SPI3_AX, sizeof(txMsg), txMsg);
        }
      }
    }

    /* VCOI Manual calibration when GPADC13 is attached to the VCO control voltage, available at FILT in external loop filter mode */
    #if defined(AX_GPADC13_ENABLED)
    {
      spi_ax_initRegisters_PR1200_Tx();

      /* MODULATION */
      {
        const uint8_t txMsg[2] = { 0x10U | C_AX_REG_WR, 0x08U };                                      // WR address 0x10: MODULATION - 08: FSK
        spiProcessSpi3MsgTemplate(SPI3_AX, sizeof(txMsg), txMsg);
      }

      /* FSKDEV */
      {
        const uint8_t txMsg[5] = { 0xf1U, 0x61U,                                                      // WR address 0x161: FSKDEV - off
            0x00U, 0x00U, 0x00U
        };
        spiProcessSpi3MsgTemplate(SPI3_AX, sizeof(txMsg), txMsg);
      }

      /* PLLLOOP */
      {
        const uint8_t txMsg[2] = { 0x30U, 0x00U };                                                    // RD address 0x38: PLLLOOP - 04: FILTEN
        spiProcessSpi3MsgTemplateLocked(SPI3_AX, sizeof(txMsg), txMsg);
        const uint8_t txMsg2[2] = { 0x30U | C_AX_REG_WR,
            0x04U | spi3RxBuffer[1]
        };                                                                                            // Write back with modified value
        osMutexRelease(spi3MutexHandle);

        spiProcessSpi3MsgTemplate(SPI3_AX, sizeof(txMsg2), txMsg2);
      }

      /* 0xF35 */
      {
        const uint8_t txMsg[3] = { 0x7fU, 0x35U, 0x00U };                                             // RD address 0xF35 (RX/TX) - Set to 0x10 for reference frequencies (crystal or TCXO) less than 24.8 MHz (fXTALDIV = 1), or to 0x11 otherwise (fXTALDIV = 2)
        spiProcessSpi3MsgTemplateLocked(SPI3_AX, sizeof(txMsg), txMsg);
        uint8_t new_0xF35 = 0x80U | spi3RxBuffer[1];
        osMutexRelease(spi3MutexHandle);

        if (0x02U & ((uint8_t) ~new_0xF35)) {
          ++new_0xF35;
        }

        const uint8_t txMsg2[3] = { 0x7fU | C_AX_REG_WR, 0x35U, new_0xF35 };                          // Write back with modified value
        spiProcessSpi3MsgTemplate(SPI3_AX, sizeof(txMsg2), tsMsg2);
      }

      /* PWRMODE */
      {
        const uint8_t txMsg[2] = { 0x02U | C_AX_REG_WR, 0x6cU };                                      // WR Address 0x02: PWRMODE - XOEN, REFEN, PWRMODE=SYNTH_TX
        spiProcessSpi3MsgTemplate(SPI3_AX, sizeof(txMsg), txMsg);
      }

      {
        /* PLLVCOI */
        uint8_t vcoi_save;
        {
          const uint8_t txMsg[3] = { 0x71U, 0x80U, 0x00U };                                           // RD address 0x180: PLLVCOI
          spiProcessSpi3MsgTemplate(SPI3_AX, sizeof(txMsg), txMsg);
          vcoi_save = spi3RdBuffer[1];
        }

        uint8_t dropFirstCalIdx = 2;
        for (uint8_t chanIdx = 0; chanIdx < 2; chanIdx++) {
          g_ax_spi_vcoi_chan[chanIdx] = 0;

          if (g_ax_spi_range_chan[chanIdx] & 0x20) {
            continue;
          }

          /* PLLRANGINGA */
          {
            const uint8_t txMsg[2] = { 0x33U | C_AX_REG_WR, g_ax_spi_range_chan[0] & 0x0fU };         // WR Address 0x33: PLLRANGINGA
            spiProcessSpi3MsgTemplate(SPI3_AX, sizeof(txMsg), txMsg);
          }

          spi_ax_setFrequency2Regs(chanIdx, chanIdx == 1 ?  1U : 0U);

          do {
            g_ax_spi_vcoi_chan[chanIdx] = spi_ax_cal_vcoi();
          } while (--dropFirstCalIdx);
          dropFirstCalIdx = 1;
        }

        /* Revert to initial setting */
        {
          const uint8_t txMsg[3] = { 0x71U | C_AX_REG_WR, 0x80U, vcoi_save };                         // WR Address 0x180: PLLVCOI
          spiProcessSpi3MsgTemplate(SPI3_AX, sizeof(txMsg), txMsg);
        }
      }
    }
    #endif  // VCOI Calibration

    /* POWERMODE POWERDOWN */
    spi_ax_setRegisters(0U, AX_SET_REGISTERS_MODULATION_INVALIDATE, AX_SET_REGISTERS_VARIANT_INVALIDATE, AX_SET_REGISTERS_POWERMODE_POWERDOWN);
  }
}

uint8_t spi_ax_vco_select(uint32_t reg_freq, uint8_t force)
{
  float f_Mhz = spi_ax_calcFrequency_Regs2MHz(reg_freq);
  uint8_t curVco2   = 0U;
  uint8_t modified  = 0U;

  /* Read VCO settings */
  {
    /* PLLVCODIV */
    const uint8_t txMsg[2] = { 0x32U | C_AX_REG_RD,
        0x00U
    };                                                                                                // RD address 0x32: PLLVCODIV - VCO2INT, VCOSEL, RFDIV
    spiProcessSpi3MsgTemplateLocked(SPI3_AX, sizeof(txMsg), txMsg, 1U);
    curVco2 = (spi3RxBuffer[1] & 0x20) ?  1U : 0U;
    osSemaphoreRelease(spi3_BSemHandle);
  }

  /* VCO1 ranges abt. 380 MHz ... 540 MHz (RFDIV=1)  and  760 MHz ... 1080 MHz (RFDIV=0) */
  if (f_Mhz >= 760.f) {
    modified = 1U;

    /* PLLVCODIV - mind you: check 0xF34, also */
    {
      const uint8_t txMsg[2] = { 0x32U | C_AX_REG_WR,
          0x00U
      };                                                                                              // WR address 0x32: PLLVCODIV - no RFDIV
      spiProcessSpi3MsgTemplate(SPI3_AX, sizeof(txMsg), txMsg);
    }

    /* 0xF34 */
    {
      const uint8_t txMsg[3] = { 0xffU, 34U,                                                          // WR address 0xF34 (RX/TX) - Set to 0x28 if RFDIV in register PLLVCODIV is set, or to 0x08 otherwise
          0x08U
      };
      spiProcessSpi3MsgTemplate(SPI3_AX, sizeof(txMsg), txMsg);
    }
  }

  else if (f_Mhz >= 380.f) {
    /* Select VCO1 */
    if (curVco2 || force) {
      modified = 1U;

      /* PLLVCODIV - mind you: check 0xF34, also */
      {
        const uint8_t txMsg[2] = { 0x32U | C_AX_REG_WR,
            0x04U
        };                                                                                            // WR address 0x32: PLLVCODIV - RFDIV
        spiProcessSpi3MsgTemplate(SPI3_AX, sizeof(txMsg), txMsg);
      }

      /* 0xF34 */
      {
        const uint8_t txMsg[3] = { 0xffU, 34U,                                                        // WR address 0xF34 (RX/TX) - Set to 0x28 if RFDIV in register PLLVCODIV is set, or to 0x08 otherwise
            0x28U
        };
        spiProcessSpi3MsgTemplate(SPI3_AX, sizeof(txMsg), txMsg);
      }
    }
  }

  else {
    /* Select VCO2 */
    if (!curVco2 || force) {
      modified = 1U;

      /* PLLVCODIV - mind you: check 0xF34, also */
      {
        const uint8_t txMsg[2] = { 0x32U | C_AX_REG_WR,
            0x34U
        };                                                                                            // WR address 0x32: PLLVCODIV - VCO2INT, VCOSEL, RFDIV
        spiProcessSpi3MsgTemplate(SPI3_AX, sizeof(txMsg), txMsg);
      }

      /* 0xF34 */
      {
        const uint8_t txMsg[3] = { 0xffU, 34U,                                                        // WR address 0xF34 (RX/TX) - Set to 0x28 if RFDIV in register PLLVCODIV is set, or to 0x08 otherwise
            0x28U
        };
        spiProcessSpi3MsgTemplate(SPI3_AX, sizeof(txMsg), txMsg);
      }
    }
  }

  return modified;
}

uint8_t spi_ax_selectVcoFreq(uint8_t isFreqB)
{
  /* Switch to VCO1 or VCO2 as needed */
  uint8_t modified = spi_ax_vco_select(s_ax_spi_freq_chan[isFreqB ?  1 : 0], 0U);

  /* PLLLOOP */
  {
    const uint8_t txMsg[2] = { 0x30U | C_AX_REG_RD,
        0x00U
    };                                                                                                // RD address 0x30: PLLLOOP
    spiProcessSpi3MsgTemplateLocked(SPI3_AX, sizeof(txMsg), txMsg, 1U);
    const uint8_t pllLoop = spi3RxBuffer[1];
    osSemaphoreRelease(spi3_BSemHandle);

    const uint8_t txMsg2[2] = { 0x30U | C_AX_REG_WR,                                                  // WR address 0x30: PLLLOOP
        (isFreqB ?  (pllLoop | 0x80)                                                                  // Set   FREQB
                 :  (pllLoop & 0x7f))
    };
    spiProcessSpi3MsgTemplate(SPI3_AX, sizeof(txMsg2), txMsg2);
  }

  return modified;
}

void spi_ax_util_FIFO_waitFree(uint8_t neededSpace)
{
  uint16_t fifoFree;

  do {
    /* FIFOFREE */
    const uint8_t txMsg[3] = { 0x2cU | C_AX_REG_RD,                                                   // RD address 0x2C: FIFOFREE
        0x00U, 0x00U
    };
    spiProcessSpi3MsgTemplateLocked(SPI3_AX, sizeof(txMsg), txMsg, 1U);
    fifoFree = 0x1ffU & (((uint16_t)spi3RxBuffer[1] << 8U) | spi3RxBuffer[2]);
    osSemaphoreRelease(spi3_BSemHandle);

    if (fifoFree >= neededSpace) {
      break;
    }

    /* Wait some time */
    osThreadYield();
  } while (1);
}

void spi_ax_setRxMode_by_MonMode(void)
{
  /* Leave when AX5243 is disabled */
  if (!s_ax5243_enable) {
    s_ax_set_mon_mode = AX_SET_MON_MODE_OFF;
    return;
  }

  AX_SET_MON_MODE_t l_ax_set_mon_mode = s_ax_set_mon_mode;

  switch (l_ax_set_mon_mode) {
    case AX_SET_MON_MODE_APRS_RX_WOR:
    case AX_SET_MON_MODE_APRS_RX_CONT:
    case AX_SET_MON_MODE_APRS_RX_CONT_SINGLEPARAMSET:
      spi_ax_setTxRxMode((AX_SET_TX_RX_MODE_t)l_ax_set_mon_mode);
      break;

    case AX_SET_MON_MODE_POCSAG_RX_WOR:
    case AX_SET_MON_MODE_POCSAG_RX_CONT:
    case AX_SET_MON_MODE_POCSAG_RX_CONT_SINGLEPARAMSET:
      spi_ax_setTxRxMode((AX_SET_TX_RX_MODE_t)l_ax_set_mon_mode);
      break;

    case AX_SET_MON_MODE_OFF:
    default:
      spi_ax_setTxRxMode(AX_SET_TX_RX_MODE_OFF);
  }
}


void spi_ax_initRegisters_FSK(void)
{
  /* MODULATION */
  {
    const uint8_t txMsg[4] = { 0x10U | C_AX_REG_WR,
        0x08U,                                                                                        // WR address 0x10: MODULATION - 08: FSK
        0x00U,                                                                                        // WR address 0x11: ENCODING - normal
        0x00U };                                                                                      // WR address 0x12: FRAMING - off
    spiProcessSpi3MsgTemplate(SPI3_AX, sizeof(txMsg), txMsg);
  }

  /* PINFUNCSYSCLK */
  {
    const uint8_t txMsg[2] = { 0x21U | C_AX_REG_WR,
        0x05U                                                                                         // WR address 0x21: PINFUNCSYSCLK - SYSCLK pin out with 8 MHz
    };
    spiProcessSpi3MsgTemplate(SPI3_AX, sizeof(txMsg), txMsg);
  }

  /* PINFUNCTCXO_EN */
  {
    const uint8_t txMsg[2] = { 0x26U | C_AX_REG_WR,
#if 0
        0x05U                                                                                         // WR address 0x26: PINFUNCTCXO_EN - Use TCXO_EN pin as DAC output
#else
        0x00U                                                                                         // WR address 0x26: PINFUNCTCXO_EN - Set to output '0'
#endif
    };
    spiProcessSpi3MsgTemplate(SPI3_AX, sizeof(txMsg), txMsg);
  }

  /* WAKEUPXOEARLY */
  {
    const uint8_t txMsg[2] = { 0x6eU | C_AX_REG_WR,
        0x01U                                                                                         // WR address 0x6E: WAKEUPXOEARLY - 1 LPOSC cycle wake-up time before receiver is started
    };
    spiProcessSpi3MsgTemplate(SPI3_AX, sizeof(txMsg), txMsg);
  }


  /* IFFREQ */
  {
    const uint8_t txMsg[4] = { 0xf1U, 0x00U,                                                          // WR address 0x100: IFFREQ - IFFREQ: 3,128 Hz (f_xtal = 16 MHz)
        0x00U, 0xcdU
    };
    spiProcessSpi3MsgTemplate(SPI3_AX, sizeof(txMsg), txMsg);
  }

  /* DECIMATION */
  {
    const uint8_t txMsg[3] = { 0xf1U, 0x02U,                                                          // WR address 0x102: DECIMATION - DECIMATION: 37d, f_BASEBAND = 27,027.03 Hz
        0x25U
    };
    spiProcessSpi3MsgTemplate(SPI3_AX, sizeof(txMsg), txMsg);
  }

  /* RXDATARATE */
  {
    const uint8_t txMsg[5] = { 0xf1U, 0x03U,                                                          // WR address 0x103: RXDATARATE - 1,200 bit/s
        0x00U, 0xb4U, 0x2eU
    };
    spiProcessSpi3MsgTemplate(SPI3_AX, sizeof(txMsg), txMsg);
  }

  /* MAXDROFFSET */
  {
    const uint8_t txMsg[5] = { 0xf1U, 0x06U,                                                          // WR address 0x106: MAXDROFFSET - off
        0x00U, 0x00U, 0x00U
    };
    spiProcessSpi3MsgTemplate(SPI3_AX, sizeof(txMsg), txMsg);
  }

  /* MAXRFOFFSET */
  {
    const uint8_t txMsg[5] = { 0xf1U, 0x09U,                                                          // WR address 0x109: MAXRFOFFSET - FREQOFFSCORR: Correct frequency offset at the first LO if this bit is one, MAXRFOFFSET: +/- 1,799.6 Hz
        0x80U, 0x07U, 0x5fU
    };
    spiProcessSpi3MsgTemplate(SPI3_AX, sizeof(txMsg), txMsg);
  }

  /* FSKDMAX */
  {
    const uint8_t txMsg[4] = { 0xf1U, 0x0cU,                                                          // WR address 0x10C: FSKDMAX - FSKDMAX: +1,011d (should be +640d?, seems to be moved by abt. 1.5x up)
        0x03U, 0xf3U
    };
    spiProcessSpi3MsgTemplate(SPI3_AX, sizeof(txMsg), txMsg);
  }

  /* FSKDMIN */
  {
    const uint8_t txMsg[4] = { 0xf1U, 0x0eU,                                                          // WR address 0x10E: FSKDMIN - FSKDMIN: -243d (should be -640d?, seems to be moved by abt. 1.5x up)
        0xffU, 0x0dU
    };
    spiProcessSpi3MsgTemplate(SPI3_AX, sizeof(txMsg), txMsg);
  }

  /* AMPLFILTER */
  {
    const uint8_t txMsg[3] = { 0xf1U, 0x15U,                                                          // WR address 0x115: AMPLFILTER - AMPLFILTER: filter bypassed.
        0x00U
    };
    spiProcessSpi3MsgTemplate(SPI3_AX, sizeof(txMsg), txMsg);
  }

  #if 0
  /* FREQUENCYLEAK */
  {
    const uint8_t txMsg[3] = { 0xf1U, 0x16U,                                                          // WR address 0x116: FREQUENCYLEAK
        0x00U
    };
    spiProcessSpi3MsgTemplate(SPI3_AX, sizeof(txMsg), txMsg);
  }
  #endif

  /* RXPARAMSETS */
  {
    const uint8_t txMsg[3] = { 0xf1U, 0x17U,                                                          // WR address 0x117: RXPARAMSETS - RXPS0: 0, RXPS1: 1, RXPS2: 3, RXPS3: 3
        0xf4U
    };
    spiProcessSpi3MsgTemplate(SPI3_AX, sizeof(txMsg), txMsg);
  }

  /* AGCGAIN0 */
  {
    const uint8_t txMsg[3] = { 0xf1U, 0x20U,                                                          // WR address 0x120: AGCGAIN0 - AGCATTACK0: 8, AGCDECAY0: 14
        0xe8U
    };
    spiProcessSpi3MsgTemplate(SPI3_AX, sizeof(txMsg), txMsg);
  }

  /* AGCTARGET0 */
  {
    const uint8_t txMsg[3] = { 0xf1U, 0x21U,                                                          // WR address 0x121: AGCTARGET0 - average AGC magnitude = 304
        0x84U
    };
    spiProcessSpi3MsgTemplate(SPI3_AX, sizeof(txMsg), txMsg);
  }

  /* TIMEGAIN0 */
  {
    const uint8_t txMsg[3] = { 0xf1U, 0x24U,                                                          // WR address 0x124: TIMEGAIN0
        0xbaU
    };
    spiProcessSpi3MsgTemplate(SPI3_AX, sizeof(txMsg), txMsg);
  }

  /* DRGAIN0  0xB4 */
  {
    const uint8_t txMsg[3] = { 0xf1U, 0x25U,                                                          // WR address 0x125: DRGAIN0
        0xb4U
    };
    spiProcessSpi3MsgTemplate(SPI3_AX, sizeof(txMsg), txMsg);
  }

  /* PHASEGAIN0 */
  {
    const uint8_t txMsg[3] = { 0xf1U, 0x26U,                                                          // WR address 0x126: PHASEGAIN0
        0xc3U
    };
    spiProcessSpi3MsgTemplate(SPI3_AX, sizeof(txMsg), txMsg);
  }

  /* FREQGAINA0 */
  {
    const uint8_t txMsg[3] = { 0xf1U, 0x27U,                                                          // WR address 0x127: FREQGAINA0
        0x0fU
    };
    spiProcessSpi3MsgTemplate(SPI3_AX, sizeof(txMsg), txMsg);
  }

  /* FREQGAINB0 */
  {
    const uint8_t txMsg[3] = { 0xf1U, 0x28U,                                                          // WR address 0x128: FREQGAINB0
        0x1fU
    };
    spiProcessSpi3MsgTemplate(SPI3_AX, sizeof(txMsg), txMsg);
  }

  /* FREQGAINC0 */
  {
    const uint8_t txMsg[3] = { 0xf1U, 0x29U,                                                          // WR address 0x129: FREQGAINC0
        0x0aU
    };
    spiProcessSpi3MsgTemplate(SPI3_AX, sizeof(txMsg), txMsg);
  }

  /* FREQGAIND0 */
  {
    const uint8_t txMsg[3] = { 0xf1U, 0x2aU,                                                          // WR address 0x12A: FREQGAIND0
        0x0aU
    };
    spiProcessSpi3MsgTemplate(SPI3_AX, sizeof(txMsg), txMsg);
  }

  /* AMPLGAIN0 */
  {
    const uint8_t txMsg[3] = { 0xf1U, 0x2bU,                                                          // WR address 0x12B: AMPLGAIN0
        0x06U
    };
    spiProcessSpi3MsgTemplate(SPI3_AX, sizeof(txMsg), txMsg);
  }

  /* FREQDEV0 */
  {
    const uint8_t txMsg[4] = { 0xf1U, 0x2cU,                                                          // WR address 0x12C: FREQDEV0
        0x00U, 0x00U
    };
    spiProcessSpi3MsgTemplate(SPI3_AX, sizeof(txMsg), txMsg);
  }

  /* BBOFFSRES0 */
  {
    const uint8_t txMsg[3] = { 0xf1U, 0x2fU,                                                          // WR address 0x12F: BBOFFSRES0
        0x00U
    };
    spiProcessSpi3MsgTemplate(SPI3_AX, sizeof(txMsg), txMsg);
  }


  /* AGCGAIN1 */
  {
    const uint8_t txMsg[3] = { 0xf1U, 0x30U,                                                          // WR address 0x130: AGCGAIN1
        0xe8U
    };
    spiProcessSpi3MsgTemplate(SPI3_AX, sizeof(txMsg), txMsg);
  }

  /* AGCTARGET1 */
  {
    const uint8_t txMsg[3] = { 0xf1U, 0x31U,                                                          // WR address 0x131: AGCTARGET1
        0x84U
    };
    spiProcessSpi3MsgTemplate(SPI3_AX, sizeof(txMsg), txMsg);
  }

  /* AGCAHYST1 */
  {
    const uint8_t txMsg[3] = { 0xf1U, 0x32U,                                                          // WR address 0x132: AGCAHYST1
        0x00U
    };
    spiProcessSpi3MsgTemplate(SPI3_AX, sizeof(txMsg), txMsg);
  }

  /* AGCMINMAX1 */
  {
    const uint8_t txMsg[3] = { 0xf1U, 0x33U,                                                          // WR address 0x133: AGCMINMAX1
        0x00U
    };
    spiProcessSpi3MsgTemplate(SPI3_AX, sizeof(txMsg), txMsg);
  }

  /* TIMEGAIN1 */
  {
    const uint8_t txMsg[3] = { 0xf1U, 0x34U,                                                          // WR address 0x134: TIMEGAIN1
        0xb8U
    };
    spiProcessSpi3MsgTemplate(SPI3_AX, sizeof(txMsg), txMsg);
  }

  /* DRGAIN1 */
  {
    const uint8_t txMsg[3] = { 0xf1U, 0x35U,                                                          // WR address 0x135: DRGAIN1
        0xb3U
    };
    spiProcessSpi3MsgTemplate(SPI3_AX, sizeof(txMsg), txMsg);
  }

  /* PHASEGAIN1 */
  {
    const uint8_t txMsg[3] = { 0xf1U, 0x36U,                                                          // WR address 0x136: PHASEGAIN1
        0xc3U
    };
    spiProcessSpi3MsgTemplate(SPI3_AX, sizeof(txMsg), txMsg);
  }

  /* FREQGAINA1 */
  {
    const uint8_t txMsg[3] = { 0xf1U, 0x37U,                                                          // WR address 0x137: FREQGAINA1
        0x0fU
    };
    spiProcessSpi3MsgTemplate(SPI3_AX, sizeof(txMsg), txMsg);
  }

  /* FREQGAINB1 */
  {
    const uint8_t txMsg[3] = { 0xf1U, 0x38U,                                                          // WR address 0x138: FREQGAINB1
        0x1fU
    };
    spiProcessSpi3MsgTemplate(SPI3_AX, sizeof(txMsg), txMsg);
  }

  /* FREQGAINC1 */
  {
    const uint8_t txMsg[3] = { 0xf1U, 0x39U,                                                          // WR address 0x139: FREQGAINC1
        0x0aU
    };
    spiProcessSpi3MsgTemplate(SPI3_AX, sizeof(txMsg), txMsg);
  }

  /* FREQGAIND1 */
  {
    const uint8_t txMsg[3] = { 0xf1U, 0x3aU,                                                          // WR address 0x13A: FREQGAIND1
        0x0aU
    };
    spiProcessSpi3MsgTemplate(SPI3_AX, sizeof(txMsg), txMsg);
  }

  /* AMPLGAIN1 */
  {
    const uint8_t txMsg[3] = { 0xf1U, 0x3bU,                                                          // WR address 0x13B: AMPLGAIN1
        0x06U
    };
    spiProcessSpi3MsgTemplate(SPI3_AX, sizeof(txMsg), txMsg);
  }

  /* FREQDEV1 */
  {
    const uint8_t txMsg[4] = { 0xf1U, 0x3cU,                                                          // WR address 0x13C: FREQDEV1
        0x00U, 0x4bU
    };
    spiProcessSpi3MsgTemplate(SPI3_AX, sizeof(txMsg), txMsg);
  }

  /* FOURFSK1 */
  {
    const uint8_t txMsg[3] = { 0xf1U, 0x3eU,                                                          // WR address 0x13E: FOURFSK1
        0x16U
    };
    spiProcessSpi3MsgTemplate(SPI3_AX, sizeof(txMsg), txMsg);
  }

  /* BBOFFSRES1 */
  {
    const uint8_t txMsg[3] = { 0xf1U, 0x3fU,                                                          // WR address 0x13F: BBOFFSRES1
        0x00U
    };
    spiProcessSpi3MsgTemplate(SPI3_AX, sizeof(txMsg), txMsg);
  }


  /* AGCGAIN3 */
  {
    const uint8_t txMsg[3] = { 0xf1U, 0x50U,                                                          // WR address 0x150: AGCGAIN3
        0xffU
    };
    spiProcessSpi3MsgTemplate(SPI3_AX, sizeof(txMsg), txMsg);
  }

  /* AGCTARGET3 */
  {
    const uint8_t txMsg[3] = { 0xf1U, 0x51U,                                                          // WR address 0x151: AGCTARGET3
        0x84U
    };
    spiProcessSpi3MsgTemplate(SPI3_AX, sizeof(txMsg), txMsg);
  }

  /* AGCAHYST3 */
  {
    const uint8_t txMsg[3] = { 0xf1U, 0x52U,                                                          // WR address 0x152: AGCAHYST3
        0x00U
    };
    spiProcessSpi3MsgTemplate(SPI3_AX, sizeof(txMsg), txMsg);
  }

  /* AGCMINMAX3 */
  {
    const uint8_t txMsg[3] = { 0xf1U, 0x53U,                                                          // WR address 0x153: AGCMINMAX3
        0x00U
    };
    spiProcessSpi3MsgTemplate(SPI3_AX, sizeof(txMsg), txMsg);
  }

  /* TIMEGAIN3 */
  {
    const uint8_t txMsg[3] = { 0xf1U, 0x54U,                                                          // WR address 0x154: TIMEGAIN3
        0xb8U
    };
    spiProcessSpi3MsgTemplate(SPI3_AX, sizeof(txMsg), txMsg);
  }

  /* DRGAIN3 */
  {
    const uint8_t txMsg[3] = { 0xf1U, 0x55U,                                                          // WR address 0x155: DRGAIN3
        0xb3U
    };
    spiProcessSpi3MsgTemplate(SPI3_AX, sizeof(txMsg), txMsg);
  }

  /* PHASEGAIN3 */
  {
    const uint8_t txMsg[3] = { 0xf1U, 0x56U,                                                          // WR address 0x156: PHASEGAIN3
        0xc3U
    };
    spiProcessSpi3MsgTemplate(SPI3_AX, sizeof(txMsg), txMsg);
  }

  /* FREQGAINA3 */
  {
    const uint8_t txMsg[3] = { 0xf1U, 0x57U,                                                          // WR address 0x157: FREQGAINA3
        0x0fU
    };
    spiProcessSpi3MsgTemplate(SPI3_AX, sizeof(txMsg), txMsg);
  }

  /* FREQGAINB3 */
  {
    const uint8_t txMsg[3] = { 0xf1U, 0x58U,                                                          // WR address 0x158: FREQGAINB3
        0x1fU
    };
    spiProcessSpi3MsgTemplate(SPI3_AX, sizeof(txMsg), txMsg);
  }

  /* FREQGAINC3 */
  {
    const uint8_t txMsg[3] = { 0xf1U, 0x59U,                                                          // WR address 0x159: FREQGAINC3
        0x0dU
    };
    spiProcessSpi3MsgTemplate(SPI3_AX, sizeof(txMsg), txMsg);
  }

  /* FREQGAIND3 */
  {
    const uint8_t txMsg[3] = { 0xf1U, 0x5aU,                                                          // WR address 0x15A: FREQGAIND3
        0x0dU
    };
    spiProcessSpi3MsgTemplate(SPI3_AX, sizeof(txMsg), txMsg);
  }

  /* AMPLGAIN3 */
  {
    const uint8_t txMsg[3] = { 0xf1U, 0x5bU,                                                          // WR address 0x15B: AMPLGAIN3
        0x06U
    };
    spiProcessSpi3MsgTemplate(SPI3_AX, sizeof(txMsg), txMsg);
  }

  /* FREQDEV3 */
  {
    const uint8_t txMsg[4] = { 0xf1U, 0x5cU,                                                          // WR address 0x15C: FREQDEV3
        0x00U, 0x04bU
    };
    spiProcessSpi3MsgTemplate(SPI3_AX, sizeof(txMsg), txMsg);
  }

  /* FOURFSK3 */
  {
    const uint8_t txMsg[3] = { 0xf1U, 0x5eU,                                                          // WR address 0x15E: FOURFSK3
        0x16U
    };
    spiProcessSpi3MsgTemplate(SPI3_AX, sizeof(txMsg), txMsg);
  }

  /* BBOFFSRES3 */
  {
    const uint8_t txMsg[3] = { 0xf1U, 0x5fU,                                                          // WR address 0x15F: BBOFFSRES3 - not used
        0x00U
    };
    spiProcessSpi3MsgTemplate(SPI3_AX, sizeof(txMsg), txMsg);
  }


  /* MODCFGF */
  {
    const uint8_t txMsg[3] = { 0xf1U, 0x60U,                                                          // WR address 0x160: MODCFGF - FREQSHAPE: External Loop Filter (BT = 0.0)
        0x00U
    };
    spiProcessSpi3MsgTemplate(SPI3_AX, sizeof(txMsg), txMsg);
  }

  /* FSKDEV */
  {
    const uint8_t txMsg[5] = { 0xf1U, 0x61U,                                                          // WR address 0x161: FSKDEV - FSKDEV: 500 Hz @ fxtal = 16 MHz.
        0x00U, 0x02U, 0x0cU
    };
    spiProcessSpi3MsgTemplate(SPI3_AX, sizeof(txMsg), txMsg);
  }


  /* MODCFGA */
  {
    const uint8_t txMsg[3] = { 0xf1U, 0x64U,                                                          // WR address 0x164: MODCFGA - AMPLSHAPE, TXDIFF
        0x05U
    };
    spiProcessSpi3MsgTemplate(SPI3_AX, sizeof(txMsg), txMsg);
  }

  /* TXRATE */
  {
    const uint8_t txMsg[5] = { 0xf1U, 0x65U,                                                          // WR address 0x165: TXRATE - TXRATE: 1,200 bit/s
        0x00U, 0x04U, 0xeaU
    };
    spiProcessSpi3MsgTemplate(SPI3_AX, sizeof(txMsg), txMsg);
  }

  /* TXPWRCOEFFA */
  {
    const uint8_t txMsg[4] = { 0xf1U, 0x68U,                                                          // WR address 0x168: TXPWRCOEFFA - no correction
        0x00U, 0x00U
    };
    spiProcessSpi3MsgTemplate(SPI3_AX, sizeof(txMsg), txMsg);
  }

  /* TXPWRCOEFFB */
  {
    const uint8_t txMsg[4] = { 0xf1U, 0x6aU,                                                          // WR address 0x16A: TXPWRCOEFFB - off
        0x00U, 0x00U
    };
    spiProcessSpi3MsgTemplate(SPI3_AX, sizeof(txMsg), txMsg);
  }

  /* TXPWRCOEFFC */
  {
    const uint8_t txMsg[4] = { 0xf1U, 0x6cU,                                                          // WR address 0x16C: TXPWRCOEFFC - no correction
        0x00U, 0x00U
    };
    spiProcessSpi3MsgTemplate(SPI3_AX, sizeof(txMsg), txMsg);
  }

  /* TXPWRCOEFFD */
  {
    const uint8_t txMsg[4] = { 0xf1U, 0x6eU,                                                          // WR address 0x16E: TXPWRCOEFFD - no correction
        0x00U, 0x00U
    };
    spiProcessSpi3MsgTemplate(SPI3_AX, sizeof(txMsg), txMsg);
  }

  /* TXPWRCOEFFE */
  {
    const uint8_t txMsg[4] = { 0xf1U, 0x70U,                                                          // WR address 0x170: TXPWRCOEFFE - no correction
        0x00U, 0x00U
    };
    spiProcessSpi3MsgTemplate(SPI3_AX, sizeof(txMsg), txMsg);
  }


  /* PLLVCOI */
  {
    const uint8_t txMsg[3] = { 0xf1U, 0x80U,                                                          // WR address 0x180: PLLVCOI - 10 µA * 153 = 1,53 mA
        0x99U
    };
    spiProcessSpi3MsgTemplate(SPI3_AX, sizeof(txMsg), txMsg);
  }

  /* PLLRNGCLK */
  {
    const uint8_t txMsg[3] = { 0xf1U, 0x83U,                                                          // WR address 0x183: PLLRNGCLK - PLLRNGCLK: 7,812 Hz ? (@see Table 148 in AND9347/D)
        0x03U
    };
    spiProcessSpi3MsgTemplate(SPI3_AX, sizeof(txMsg), txMsg);
  }

  /* BBTUNE */
  {
    const uint8_t txMsg[3] = { 0xf1U, 0x88U,                                                          // WR address 0x188: BBTUNE - BBTUNE: 15 (?)
        0x0fU
    };
    spiProcessSpi3MsgTemplate(SPI3_AX, sizeof(txMsg), txMsg);
  }

  /* BBOFFSCAP */
  {
    const uint8_t txMsg[3] = { 0xf1U, 0x89U,                                                          // WR address 0x189: BBOFFSCAP - CAPINTB: 7, CAPINTA: 7
        0x77U
    };
    spiProcessSpi3MsgTemplate(SPI3_AX, sizeof(txMsg), txMsg);
  }


  /* TMGTXBOOST */
  {
    const uint8_t txMsg[3] = { 0xf2U, 0x20U,                                                          // WR address 0x220: TMGTXBOOST - TMGTXBOOSTE = 1, TMGTXBOOSTM = 18 --> 36 µs
        0x32U
    };
    spiProcessSpi3MsgTemplate(SPI3_AX, sizeof(txMsg), txMsg);
  }

  /* TMGTXSETTLE */
  {
    const uint8_t txMsg[3] = { 0xf2U, 0x21U,                                                          // WR address 0x221: TMGTXSETTLE - TMGTXSETTLEE = 0, TMGTXSETTLEM = 20 --> 20 µs
        0x14U
    };
    spiProcessSpi3MsgTemplate(SPI3_AX, sizeof(txMsg), txMsg);
  }

  /* TMGRXBOOST */
  {
    const uint8_t txMsg[3] = { 0xf2U, 0x23U,                                                          // WR address 0x223: TMGRXBOOST - TMGRXBOOSTE = 1, TMGRXBOOSTM = 18 --> 36 µs
        0x32U
    };
    spiProcessSpi3MsgTemplate(SPI3_AX, sizeof(txMsg), txMsg);
  }

  /* TMGRXSETTLE */
  {
    const uint8_t txMsg[3] = { 0xf2U, 0x24U,                                                          // WR address 0x224: TMGRXSETTLE - TMGRXSETTLEE = 0, TMGRXSETTLEM = 20 --> 20 µs
        0x14U
    };
    spiProcessSpi3MsgTemplate(SPI3_AX, sizeof(txMsg), txMsg);
  }

  /* TMGRXOFFSACQ */
  {
    const uint8_t txMsg[3] = { 0xf2U, 0x25U,                                                          // WR address 0x225: TMGRXOFFSACQ - TMGRXOFFSACQE = 0, TMGRXOFFSACQM = 0 --> 0 µs
        0x00U
    };
    spiProcessSpi3MsgTemplate(SPI3_AX, sizeof(txMsg), txMsg);
  }

  /* TMGRXCOARSEAGC */
  {
    const uint8_t txMsg[3] = { 0xf2U, 0x26U,                                                          // WR address 0x226: TMGRXCOARSEAGC - TMGRXCOARSEAGCE = 3, TMGRXCOARSEAGCM = 19 --> 152 µs (Bits)  @see PKTMISCFLAGS.RXAGC
        0x73U
    };
    spiProcessSpi3MsgTemplate(SPI3_AX, sizeof(txMsg), txMsg);
  }

  /* TMGRXRSSI */
  {
    const uint8_t txMsg[3] = { 0xf2U, 0x28U,                                                          // WR address 0x228: TMGRXRSSI - TMGRXAGCE = 0, TMGRXAGCM = 3 --> 3 µs (Bits)  @see PKTMISCFLAGS.RXRSSI
        0x03U
    };
    spiProcessSpi3MsgTemplate(SPI3_AX, sizeof(txMsg), txMsg);
  }

  /* TMGRXPREAMBLE1 */
#if 0
  {
    const uint8_t txMsg[3] = { 0xf2U, 0x29U,                                                          // WR address 0x229: TMGRXPREAMBLE1 - TMGRXPREAMBLE1 timeout = none
        0x00U
    };
    spiProcessSpi3MsgTemplate(SPI3_AX, sizeof(txMsg), txMsg);
  }
#endif

  /* TMGRXPREAMBLE2 */
  {
    const uint8_t txMsg[3] = { 0xf2U, 0x2aU,                                                          // WR address 0x22A: TMGRXPREAMBLE2 - TMGRXPREAMBLE2 timeout = 7 * 2^1 = 14 bits
        0x17U
    };
    spiProcessSpi3MsgTemplate(SPI3_AX, sizeof(txMsg), txMsg);
  }

  /* TMGRXPREAMBLE3 */
#if 0
  {
    const uint8_t txMsg[3] = { 0xf2U, 0x2bU,                                                          // WR address 0x22B: TMGRXPREAMBLE3 - TMGRXPREAMBLE3 timeout = none
        0x00U
    };
    spiProcessSpi3MsgTemplate(SPI3_AX, sizeof(txMsg), txMsg);
  }
#endif

  /* RSSIREFERENCE */
  {
    const uint8_t txMsg[3] = { 0xf2U, 0x2cU,                                                          // WR address 0x22C: RSSIREFERENCE - RSSI Offset, this register adds a constant offset to the computed RSSI value. It is used to compensate for board effects.
        0xf8U
    };
    spiProcessSpi3MsgTemplate(SPI3_AX, sizeof(txMsg), txMsg);
  }

  /* RSSIABSTHR */
  {
    const uint8_t txMsg[3] = { 0xf2U, 0x2dU,                                                          // WR address 0x22D: RSSIABSTHR - RSSIABSTHR > -35 (-64) = -99 dBm (BUSY)
        0xddU
    };
    spiProcessSpi3MsgTemplate(SPI3_AX, sizeof(txMsg), txMsg);
  }

  /* BGNDRSSITHR */
  {
    const uint8_t txMsg[3] = { 0xf2U, 0x2fU,                                                          // WR address 0x22F: BGNDRSSITHR - BGNDRSSITHR: off
        0x00U
    };
    spiProcessSpi3MsgTemplate(SPI3_AX, sizeof(txMsg), txMsg);
  }


  /* PKTMISCFLAGS */
  {
    const uint8_t txMsg[3] = { 0xf2U, 0x31U,                                                          // WR address 0x231: PKTMISCFLAGS - no BGND RSSI, RXAGC CLK, RXRSSI CLK clock sources: 1 µs
        0x00U
    };
    spiProcessSpi3MsgTemplate(SPI3_AX, sizeof(txMsg), txMsg);
  }


  /* LPOSCCONFIG */
  {
    const uint8_t txMsg[3] = { 0xf3U, 0x10U,                                                          // WR address 0x310: LPOSCCONFIG - LPOSC CALIBF 0x10, LPOSC FAST 0x02, (LPOSC ENA 0x01)
        0x12U
    };
    spiProcessSpi3MsgTemplate(SPI3_AX, sizeof(txMsg), txMsg);
  }

  /* LPOSCKFILT */
  {
    const uint8_t txMsg[4] = { 0xf3U, 0x12U,                                                          // WR address 0x312: LPOSCKFILT - LPOSCKFILT <= 1,398 (lower value gives lower jitter; 1/4 th taken: 349)
        0x01U, 0x5dU
    };
    spiProcessSpi3MsgTemplate(SPI3_AX, sizeof(txMsg), txMsg);
  }

  /* LPOSCREF */
  {
    const uint8_t txMsg[4] = { 0xf3U, 0x14U,                                                          // WR address 0x314: LPOSCREF - LPOSCREF = 25,000
        0x61U, 0xa8U
    };
    spiProcessSpi3MsgTemplate(SPI3_AX, sizeof(txMsg), txMsg);
  }

  /* LPOSCFREQ */
  {
    const uint8_t txMsg[4] = { 0xf3U, 0x16U,                                                          // WR address 0x316: LPOSCFREQ - no manual tune, done by automatic
        0x00U, 0x00U
    };
    spiProcessSpi3MsgTemplate(SPI3_AX, sizeof(txMsg), txMsg);
  }


  #if 1
  /* DACVALUE */
  {
    const uint8_t txMsg[4] = { 0xf3U, 0x30U,                                                          // WR address 0x330: DACVALUE - DACSHIFT = 12 bit
        0x00U, 0x0cU
    };
    spiProcessSpi3MsgTemplate(SPI3_AX, sizeof(txMsg), txMsg);
  }

  /* DACCONFIG */
  {
    const uint8_t txMsg[3] = { 0xf3U, 0x32U,                                                          // WR address 0x332: DACCONFIG - DACPWM, DACINPUT=TRKFREQUENCY
        0x83U
    };
    spiProcessSpi3MsgTemplate(SPI3_AX, sizeof(txMsg), txMsg);
  }
  #endif


#if 0
  /* 0xF10 - XTALOSC*/
  {
    const uint8_t txMsg[3] = { 0xffU, 0x10U,                                                          // WR address 0xF10: XTALOSC
        0x03U
    };
    spiProcessSpi3MsgTemplate(SPI3_AX, sizeof(txMsg), txMsg);
  }

  /* 0xF11 - XTALAMPL */
  {
    const uint8_t txMsg[3] = { 0xffU, 0x11U,                                                          // WR address 0xF11: XTALAMPL
        0x07U
    };
    spiProcessSpi3MsgTemplate(SPI3_AX, sizeof(txMsg), txMsg);
  }
#endif
}

void spi_ax_initRegisters_FSK_Tx(void)
{
  /* XTALCAP (FSK-TX) */
  {
    const uint8_t txMsg[3] = { 0xf1U, 0x84U,                                                          // WR address 0x184: XTALCAP = 16.000018 MHz
        0x04U
    };
    spiProcessSpi3MsgTemplate(SPI3_AX, sizeof(txMsg), txMsg);
  }

#if 0
  /* PLLLOOP */
  {
    const uint8_t txMsg[2] = { 0x30U | C_AX_REG_WR,                                                   // WR address 0x30: PLLLOOP - DIRECT 0x08, no FILTEN, FLT 02: Internal Loop Filter x2 (BW = 200 kHz for ICP = 272 mA)
        0x0aU
    };
    spiProcessSpi3MsgTemplate(SPI3_AX, sizeof(txMsg), txMsg);
  }

  /* PLLLOOPBOOST */
  {
    const uint8_t txMsg[2] = { 0x38U | C_AX_REG_WR,                                                   // WR address 0x38: PLLLOOPBOOST - DIRECT 0x08, no FILTEN, FLT 03: Internal Loop Filter x5 (BW = 500 kHz for ICP = 1.7 mA)
        0x0bU
    };
    spiProcessSpi3MsgTemplate(SPI3_AX, sizeof(txMsg), txMsg);
  }
#endif
}

void spi_ax_initRegisters_FSK_Rx(void)
{
  /* XTALCAP (FSK-RX) */
  {
    const uint8_t txMsg[3] = { 0xf1U, 0x84U,                                                          // WR address 0x184: XTALCAP = 16.000018 MHz
        0x04U
    };
    spiProcessSpi3MsgTemplate(SPI3_AX, sizeof(txMsg), txMsg);
  }

#if 0
  /* PLLLOOP */
  {
    const uint8_t txMsg[2] = { 0x30U | C_AX_REG_WR,                                                   // WR address 0x30: PLLLOOP - DIRECT 0x08, no FILTEN, FLT 02: Internal Loop Filter x2 (BW = 200 kHz for ICP = 272 mA)
        0x0aU
    };
    spiProcessSpi3MsgTemplate(SPI3_AX, sizeof(txMsg), txMsg);
  }

  /* PLLLOOPBOOST */
  {
    const uint8_t txMsg[2] = { 0x38U | C_AX_REG_WR,                                                   // WR address 0x38: PLLLOOPBOOST - DIRECT 0x08, no FILTEN, FLT 03: Internal Loop Filter x5 (BW = 500 kHz for ICP = 1.7 mA)
        0x0bU
    };
    spiProcessSpi3MsgTemplate(SPI3_AX, sizeof(txMsg), txMsg);
  }
#endif
}

void spi_ax_init_FSK_Tx(void)
{
  /* Syncing and sending reset command, then setting the default values */
  spi_ax_setRegisters(1U, AX_SET_REGISTERS_MODULATION_INVALIDATE, AX_SET_REGISTERS_VARIANT_INVALIDATE, AX_SET_REGISTERS_POWERMODE_POWERDOWN);

  /* Frequency settings */
  {
    /* FSK */
    s_ax_spi_freq_chan[0] = spi_ax_calcFrequency_Mhz2Regs(433.9250);                                  // VCO1 (internal without ext. L) with RFDIV --> VCORA = 0x09
    /*
    Radiometrix TXL2/RXL2 - 16kbps bi-phase FSK
    433.925MHz - CHAN0
    433.285MHz - CHAN1
    433.605MHz - CHAN2
    434.245MHz - CHAN3
    434.565MHz - CHAN4
    */

    /* POCSAG */
    s_ax_spi_freq_chan[1] = spi_ax_calcFrequency_Mhz2Regs(439.9875);                                  // VCO1 (internal without ext. L) with RFDIV --> VCORB = 0x09

    /* FREQA <-- chan[0], FREQB <-- chan[1] */
    spi_ax_setFrequency2Regs(0, 0U);
    spi_ax_setFrequency2Regs(1, 1U);

    /* @see AND9347/D, page 12: Preparation 4. */
    /* Auto ranging and storing */
    spi_ax_doRanging();
  }

  /* Load the transmitter settings */
  spi_ax_setRegisters(0U, AX_SET_REGISTERS_MODULATION_FSK, AX_SET_REGISTERS_VARIANT_TX, AX_SET_REGISTERS_POWERMODE_POWERDOWN);

  #if 1
    /* Set VCO-PLL to FREQA - 433.9250 MHz */
    (void) spi_ax_selectVcoFreq(0U);
  #else
    /* Set VCO-PLL to FREQB - 439.9875 MHz */
    (void) spi_ax_selectVcoFreq(1U);
  #endif

  /* Set power level */
  spi_ax_setPower_dBm(-10.0f);

  /* FIFOCMD / FIFOSTAT */
  spi_ax_FIFO_CLEAR();

  /* Enabling the transmitter */
  spi_ax_setRegisters(0U, AX_SET_REGISTERS_MODULATION_NO_CHANGE, AX_SET_REGISTERS_VARIANT_NO_CHANGE, AX_SET_REGISTERS_POWERMODE_FULLTX);
}

void spi_ax_init_FSK_Rx(void)
{
  /* Syncing and sending reset command, then setting the default values */
  spi_ax_setRegisters(1U, AX_SET_REGISTERS_MODULATION_INVALIDATE, AX_SET_REGISTERS_VARIANT_INVALIDATE, AX_SET_REGISTERS_POWERMODE_POWERDOWN);

  /* Frequency settings */
  {
    /* FSK */
    s_ax_spi_freq_chan[0] = spi_ax_calcFrequency_Mhz2Regs(433.9250);                                  // VCO1 (internal without ext. L) with RFDIV --> VCORA = 0x09
    /*
    Radiometrix TXL2/RXL2 - 16kbps bi-phase FSK
    433.925MHz - CHAN0
    433.285MHz - CHAN1
    433.605MHz - CHAN2
    434.245MHz - CHAN3
    434.565MHz - CHAN4
    */

    /* POCSAG */
    s_ax_spi_freq_chan[1] = spi_ax_calcFrequency_Mhz2Regs(439.9875);                                  // VCO1 (internal without ext. L) with RFDIV --> VCORB = 0x09

    /* FREQA <-- chan[0], FREQB <-- chan[1] */
    spi_ax_setFrequency2Regs(0, 0U);
    spi_ax_setFrequency2Regs(1, 1U);

    /* @see AND9347/D, page 12: Preparation 4. */
    /* Auto ranging and storing */
    spi_ax_doRanging();
  }

  /* Load the receiver settings */
  spi_ax_setRegisters(0U, AX_SET_REGISTERS_MODULATION_FSK, AX_SET_REGISTERS_VARIANT_RX_WOR, AX_SET_REGISTERS_POWERMODE_POWERDOWN);

  #if 0
  /* Set VCO-PLL to FREQA - 433.9250 MHz */
  (void) spi_ax_selectVcoFreq(0U);
  #else
  /* Set VCO-PLL to FREQB - 439.9875 MHz */
  (void) spi_ax_selectVcoFreq(1U);
  #endif

  /* FIFOCMD / FIFOSTAT */
  spi_ax_FIFO_CLEAR();

  /* Enabling the wake-on-radio receiver */
  spi_ax_setRegisters(0U, AX_SET_REGISTERS_MODULATION_NO_CHANGE, AX_SET_REGISTERS_VARIANT_NO_CHANGE, AX_SET_REGISTERS_POWERMODE_WOR);
}


void spi_ax_initRegisters_PR1200(void)
{
  /* MODULATION */
  {
    const uint8_t txMsg[2] = { 0x10U | C_AX_REG_WR,                                                   // WR address 0x10: MODULATION - 0A: AFSK
        0x0aU
    };
    spiProcessSpi3MsgTemplate(SPI3_AX, sizeof(txMsg), txMsg);
  }

  /* ENCODING */
  {
    const uint8_t txMsg[2] = { 0x11U | C_AX_REG_WR,                                                   // WR address 0x11: ENCODING -  NRZI = ENC DIFF 0x02  &  ENC INV 0x01
        0x03U
    };
    spiProcessSpi3MsgTemplate(SPI3_AX, sizeof(txMsg), txMsg);
  }

  /* FRAMING */
  /* When FRMMODE: "Raw, Soft Bits (0b001 << 1)" is selected, do address 0xF72 also */
  {
    const uint8_t txMsg[2] = { 0x12U | C_AX_REG_WR,
        0x14U                                                                                         // WR address 0x12: FRAMING - CRCMODE: CCITT (16 bit) 0x10 (right for AX.25), FRMMODE: HDLC [1] 0x04      --> with automatic ending CRC, Flag and 16x '1's, 2xSPACE, off
      //0x10U                                                                                         // WR address 0x12: FRAMING - CRCMODE: CCITT (16 bit) 0x10 (right for AX.25), FRMMODE: Raw 0x00         --> no automatic ending Flag, 2xSPACE, off
      //0x12U                                                                                         // WR address 0x12: FRAMING - CRCMODE: CCITT (16 bit) 0x10 (right for AX.25), FRMMODE: Raw, Soft Bits 0x02    --> no automatic ending Flag, 2xSPACE, off
      //0x16U                                                                                         // WR address 0x12: FRAMING - CRCMODE: CCITT (16 bit) 0x10 (right for AX.25), FRMMODE: Raw, Pattern Match 0x06  --> no automatic ending Flag, 2xSPACE, off
      //0x04U                                                                                         // WR address 0x12: FRAMING - CRCMODE: none 0x00, FRMMODE: HDLC [1] 0x04
      //0x24U                                                                                         // WR address 0x12: FRAMING - CRCMODE: CRC-16 0x20 (wrong for AX.25), FRMMODE: HDLC [1] 0x04
    };
    spiProcessSpi3MsgTemplate(SPI3_AX, sizeof(txMsg), txMsg);
  }

  /* CRCINIT */
  {
    const uint8_t txMsg[5] = { 0x14U | C_AX_REG_WR,                                                   // WR address 0x14: CRCINIT
        0xffU, 0xffU, 0xffU, 0xffU
    };
    spiProcessSpi3MsgTemplate(SPI3_AX, sizeof(txMsg), txMsg);
  }

  /* PINFUNCSYSCLK */
  {
    const uint8_t txMsg[2] = { 0x21U | C_AX_REG_WR,
        0x05U                                                                                         // WR address 0x21: PINFUNCSYSCLK - SYSCLK pin out with 8 MHz
    };
    spiProcessSpi3MsgTemplate(SPI3_AX, sizeof(txMsg), txMsg);
  }

  /*WAKEUPTIMER */
#if 0
  uint16_t wutNext;
  {
    const uint8_t txMsg[3] = { 0x68U,                                                                 // RD address 0x68: WAKEUPTIMER
        0x00U, 0x00U
    };
    spiProcessSpi3MsgTemplateLocked(SPI3_AX, sizeof(txMsg), txMsg);
    wutNext = ((uint16_t)spi3RxBuffer[1] << 8) | spi3RxBuffer[2];
    wutNext += 1024;
    osMutexRelease(spi3MutexHandle);
  }

  {
    const uint8_t txMsg[3] = { 0x6aU | C_AX_REG_WR,                                                   // WR address 0x6A: WAKEUP - 100 ms later
        wutNext >> 8, wutNext & 0xff
    };
    spiProcessSpi3MsgTemplate(SPI3_AX, sizeof(txMsg), txMsg);
  }
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
