DF4IAH/HFT-Core-Module/SW/HFT-Core-Module_TrueSTUDIO/Core/Src/adc.c

/**
  ******************************************************************************
  * File Name          : ADC.c
  * Description        : This file provides code for the configuration
  *                      of the ADC instances.
  ******************************************************************************
  * This notice applies to any and all portions of this file
  * that are not between comment pairs USER CODE BEGIN and
  * USER CODE END. Other portions of this file, whether 
  * inserted by the user or by software development tools
  * are owned by their respective copyright owners.
  *
  * Copyright (c) 2018 STMicroelectronics International N.V. 
  * All rights reserved.
  *
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
  ******************************************************************************
  */

/* Includes ------------------------------------------------------------------*/
#include "adc.h"

#include "gpio.h"
#include "dma.h"

/* USER CODE BEGIN 0 */
extern uint32_t                       g_main_adc1_clkpresclr;
extern uint32_t                       g_main_adc3_clkpresclr;

#ifdef STMSTD
/* USER CODE END 0 */

ADC_HandleTypeDef hadc1;
ADC_HandleTypeDef hadc3;
DMA_HandleTypeDef hdma_adc1;
DMA_HandleTypeDef hdma_adc3;

/* ADC1 init function */
void MX_ADC1_Init(void)
{
  ADC_MultiModeTypeDef multimode;
  ADC_ChannelConfTypeDef sConfig;

    /**Common config 
    */
  hadc1.Instance = ADC1;
  hadc1.Init.ClockPrescaler = ADC_CLOCK_ASYNC_DIV1;
  hadc1.Init.Resolution = ADC_RESOLUTION_12B;
  hadc1.Init.DataAlign = ADC_DATAALIGN_RIGHT;
  hadc1.Init.ScanConvMode = ADC_SCAN_ENABLE;
  hadc1.Init.EOCSelection = ADC_EOC_SINGLE_CONV;
  hadc1.Init.LowPowerAutoWait = DISABLE;
  hadc1.Init.ContinuousConvMode = DISABLE;
  hadc1.Init.NbrOfConversion = 4;
  hadc1.Init.DiscontinuousConvMode = DISABLE;
  hadc1.Init.NbrOfDiscConversion = 1;
  hadc1.Init.ExternalTrigConv = ADC_SOFTWARE_START;
  hadc1.Init.ExternalTrigConvEdge = ADC_EXTERNALTRIGCONVEDGE_NONE;
  hadc1.Init.DMAContinuousRequests = ENABLE;
  hadc1.Init.Overrun = ADC_OVR_DATA_PRESERVED;
  hadc1.Init.OversamplingMode = ENABLE;
  hadc1.Init.Oversampling.Ratio = ADC_OVERSAMPLING_RATIO_16;
  hadc1.Init.Oversampling.RightBitShift = ADC_RIGHTBITSHIFT_NONE;
  hadc1.Init.Oversampling.TriggeredMode = ADC_TRIGGEREDMODE_SINGLE_TRIGGER;
  hadc1.Init.Oversampling.OversamplingStopReset = ADC_REGOVERSAMPLING_CONTINUED_MODE;
  if (HAL_ADC_Init(&hadc1) != HAL_OK)
  {
    _Error_Handler(__FILE__, __LINE__);
  }

    /**Configure the ADC multi-mode 
    */
  multimode.Mode = ADC_MODE_INDEPENDENT;
  if (HAL_ADCEx_MultiModeConfigChannel(&hadc1, &multimode) != HAL_OK)
  {
    _Error_Handler(__FILE__, __LINE__);
  }

    /**Configure Regular Channel 
    */
  sConfig.Channel = ADC_CHANNEL_VREFINT;
  sConfig.Rank = ADC_REGULAR_RANK_1;
  sConfig.SamplingTime = ADC_SAMPLETIME_12CYCLES_5;
  sConfig.SingleDiff = ADC_SINGLE_ENDED;
  sConfig.OffsetNumber = ADC_OFFSET_NONE;
  sConfig.Offset = 0;
  if (HAL_ADC_ConfigChannel(&hadc1, &sConfig) != HAL_OK)
  {
    _Error_Handler(__FILE__, __LINE__);
  }

    /**Configure Regular Channel 
    */
  sConfig.Channel = ADC_CHANNEL_8;
  sConfig.Rank = ADC_REGULAR_RANK_2;
  if (HAL_ADC_ConfigChannel(&hadc1, &sConfig) != HAL_OK)
  {
    _Error_Handler(__FILE__, __LINE__);
  }

    /**Configure Regular Channel 
    */
  sConfig.Channel = ADC_CHANNEL_VBAT;
  sConfig.Rank = ADC_REGULAR_RANK_3;
  sConfig.SamplingTime = ADC_SAMPLETIME_247CYCLES_5;
  if (HAL_ADC_ConfigChannel(&hadc1, &sConfig) != HAL_OK)
  {
    _Error_Handler(__FILE__, __LINE__);
  }

    /**Configure Regular Channel 
    */
  sConfig.Channel = ADC_CHANNEL_TEMPSENSOR;
  sConfig.Rank = ADC_REGULAR_RANK_4;
  sConfig.SamplingTime = ADC_SAMPLETIME_12CYCLES_5;
  if (HAL_ADC_ConfigChannel(&hadc1, &sConfig) != HAL_OK)
  {
    _Error_Handler(__FILE__, __LINE__);
  }

}
/* ADC3 init function */
void MX_ADC3_Init(void)
{
  ADC_ChannelConfTypeDef sConfig;

    /**Common config 
    */
  hadc3.Instance = ADC3;
  hadc3.Init.ClockPrescaler = ADC_CLOCK_ASYNC_DIV1;
  hadc3.Init.Resolution = ADC_RESOLUTION_12B;
  hadc3.Init.DataAlign = ADC_DATAALIGN_RIGHT;
  hadc3.Init.ScanConvMode = ADC_SCAN_DISABLE;
  hadc3.Init.EOCSelection = ADC_EOC_SINGLE_CONV;
  hadc3.Init.LowPowerAutoWait = DISABLE;
  hadc3.Init.ContinuousConvMode = DISABLE;
  hadc3.Init.NbrOfConversion = 1;
  hadc3.Init.DiscontinuousConvMode = DISABLE;
  hadc3.Init.NbrOfDiscConversion = 1;
  hadc3.Init.ExternalTrigConv = ADC_SOFTWARE_START;
  hadc3.Init.ExternalTrigConvEdge = ADC_EXTERNALTRIGCONVEDGE_NONE;
  hadc3.Init.DMAContinuousRequests = ENABLE;
  hadc3.Init.Overrun = ADC_OVR_DATA_PRESERVED;
  hadc3.Init.OversamplingMode = ENABLE;
  hadc3.Init.Oversampling.Ratio = ADC_OVERSAMPLING_RATIO_16;
  hadc3.Init.Oversampling.RightBitShift = ADC_RIGHTBITSHIFT_NONE;
  hadc3.Init.Oversampling.TriggeredMode = ADC_TRIGGEREDMODE_SINGLE_TRIGGER;
  hadc3.Init.Oversampling.OversamplingStopReset = ADC_REGOVERSAMPLING_CONTINUED_MODE;
  if (HAL_ADC_Init(&hadc3) != HAL_OK)
  {
    _Error_Handler(__FILE__, __LINE__);
  }

    /**Configure Regular Channel 
    */
  sConfig.Channel = ADC_CHANNEL_6;
  sConfig.Rank = ADC_REGULAR_RANK_1;
  sConfig.SamplingTime = ADC_SAMPLETIME_2CYCLES_5;
  sConfig.SingleDiff = ADC_SINGLE_ENDED;
  sConfig.OffsetNumber = ADC_OFFSET_NONE;
  sConfig.Offset = 0;
  if (HAL_ADC_ConfigChannel(&hadc3, &sConfig) != HAL_OK)
  {
    _Error_Handler(__FILE__, __LINE__);
  }

}

static uint32_t HAL_RCC_ADC_CLK_ENABLED=0;

void HAL_ADC_MspInit(ADC_HandleTypeDef* adcHandle)
{

  GPIO_InitTypeDef GPIO_InitStruct;
  if(adcHandle->Instance==ADC1)
  {
  /* USER CODE BEGIN ADC1_MspInit 0 */
#else

    ADC_HandleTypeDef hadc1;
    ADC_HandleTypeDef hadc3;
    DMA_HandleTypeDef hdma_adc1;
    DMA_HandleTypeDef hdma_adc3;

    /* ADC1 init function */
    void MX_ADC1_Init(void)
    {
      ADC_MultiModeTypeDef multimode;
      ADC_ChannelConfTypeDef sConfig;

        /**Common config
        */
      hadc1.Instance = ADC1;
      hadc1.Init.ClockPrescaler = g_main_adc1_clkpresclr;
      hadc1.Init.Resolution = ADC_RESOLUTION_12B;
      hadc1.Init.DataAlign = ADC_DATAALIGN_RIGHT;
      hadc1.Init.ScanConvMode = ADC_SCAN_ENABLE;
      hadc1.Init.EOCSelection = ADC_EOC_SINGLE_CONV;
      hadc1.Init.LowPowerAutoWait = DISABLE;
      hadc1.Init.ContinuousConvMode = DISABLE;
      hadc1.Init.NbrOfConversion = 4;
      hadc1.Init.DiscontinuousConvMode = DISABLE;
      hadc1.Init.NbrOfDiscConversion = 1;
      hadc1.Init.ExternalTrigConv = ADC_SOFTWARE_START;
      hadc1.Init.ExternalTrigConvEdge = ADC_EXTERNALTRIGCONVEDGE_NONE;
      hadc1.Init.DMAContinuousRequests = ENABLE;
      hadc1.Init.Overrun = ADC_OVR_DATA_PRESERVED;
      hadc1.Init.OversamplingMode = ENABLE;
      hadc1.Init.Oversampling.Ratio = ADC_OVERSAMPLING_RATIO_16;
      hadc1.Init.Oversampling.RightBitShift = ADC_RIGHTBITSHIFT_NONE;
      hadc1.Init.Oversampling.TriggeredMode = ADC_TRIGGEREDMODE_SINGLE_TRIGGER;
      hadc1.Init.Oversampling.OversamplingStopReset = ADC_REGOVERSAMPLING_CONTINUED_MODE;
      if (HAL_ADC_Init(&hadc1) != HAL_OK)
      {
        _Error_Handler(__FILE__, __LINE__);
      }

        /**Configure the ADC multi-mode
        */
      multimode.Mode = ADC_MODE_INDEPENDENT;
      if (HAL_ADCEx_MultiModeConfigChannel(&hadc1, &multimode) != HAL_OK)
      {
        _Error_Handler(__FILE__, __LINE__);
      }

        /**Configure Regular Channel
        */
      sConfig.Channel = ADC_CHANNEL_VREFINT;
      sConfig.Rank = ADC_REGULAR_RANK_1;
      sConfig.SamplingTime = ADC_SAMPLETIME_12CYCLES_5;
      sConfig.SingleDiff = ADC_SINGLE_ENDED;
      sConfig.OffsetNumber = ADC_OFFSET_NONE;
      sConfig.Offset = 0;
      if (HAL_ADC_ConfigChannel(&hadc1, &sConfig) != HAL_OK)
      {
        _Error_Handler(__FILE__, __LINE__);
      }

        /**Configure Regular Channel
        */
      sConfig.Channel = ADC_CHANNEL_8;
      sConfig.Rank = ADC_REGULAR_RANK_2;
      if (HAL_ADC_ConfigChannel(&hadc1, &sConfig) != HAL_OK)
      {
        _Error_Handler(__FILE__, __LINE__);
      }

        /**Configure Regular Channel
        */
      sConfig.Channel = ADC_CHANNEL_VBAT;
      sConfig.Rank = ADC_REGULAR_RANK_3;
      sConfig.SamplingTime = ADC_SAMPLETIME_247CYCLES_5;
      if (HAL_ADC_ConfigChannel(&hadc1, &sConfig) != HAL_OK)
      {
        _Error_Handler(__FILE__, __LINE__);
      }

        /**Configure Regular Channel
        */
      sConfig.Channel = ADC_CHANNEL_TEMPSENSOR;
      sConfig.Rank = ADC_REGULAR_RANK_4;
      sConfig.SamplingTime = ADC_SAMPLETIME_12CYCLES_5;
      if (HAL_ADC_ConfigChannel(&hadc1, &sConfig) != HAL_OK)
      {
        _Error_Handler(__FILE__, __LINE__);
      }

    }
    /* ADC3 init function */
    void MX_ADC3_Init(void)
    {
      ADC_ChannelConfTypeDef sConfig;

        /**Common config
        */
      hadc3.Instance = ADC3;
      hadc3.Init.ClockPrescaler = g_main_adc3_clkpresclr;
      hadc3.Init.Resolution = ADC_RESOLUTION_12B;
      hadc3.Init.DataAlign = ADC_DATAALIGN_RIGHT;
      hadc3.Init.ScanConvMode = ADC_SCAN_DISABLE;
      hadc3.Init.EOCSelection = ADC_EOC_SINGLE_CONV;
      hadc3.Init.LowPowerAutoWait = DISABLE;
      hadc3.Init.ContinuousConvMode = DISABLE;
      hadc3.Init.NbrOfConversion = 1;
      hadc3.Init.DiscontinuousConvMode = DISABLE;
      hadc3.Init.NbrOfDiscConversion = 1;
      hadc3.Init.ExternalTrigConv = ADC_SOFTWARE_START;
      hadc3.Init.ExternalTrigConvEdge = ADC_EXTERNALTRIGCONVEDGE_NONE;
      hadc3.Init.DMAContinuousRequests = ENABLE;
      hadc3.Init.Overrun = ADC_OVR_DATA_PRESERVED;
      hadc3.Init.OversamplingMode = ENABLE;
      hadc3.Init.Oversampling.Ratio = ADC_OVERSAMPLING_RATIO_16;
      hadc3.Init.Oversampling.RightBitShift = ADC_RIGHTBITSHIFT_NONE;
      hadc3.Init.Oversampling.TriggeredMode = ADC_TRIGGEREDMODE_SINGLE_TRIGGER;
      hadc3.Init.Oversampling.OversamplingStopReset = ADC_REGOVERSAMPLING_CONTINUED_MODE;
      if (HAL_ADC_Init(&hadc3) != HAL_OK)
      {
        _Error_Handler(__FILE__, __LINE__);
      }

        /**Configure Regular Channel
        */
      sConfig.Channel = ADC_CHANNEL_6;
      sConfig.Rank = ADC_REGULAR_RANK_1;
      sConfig.SamplingTime = ADC_SAMPLETIME_2CYCLES_5;
      sConfig.SingleDiff = ADC_SINGLE_ENDED;
      sConfig.OffsetNumber = ADC_OFFSET_NONE;
      sConfig.Offset = 0;
      if (HAL_ADC_ConfigChannel(&hadc3, &sConfig) != HAL_OK)
      {
        _Error_Handler(__FILE__, __LINE__);
      }

    }

static uint32_t HAL_RCC_ADC_CLK_ENABLED=0;

void HAL_ADC_MspInit(ADC_HandleTypeDef* adcHandle)
{

  GPIO_InitTypeDef GPIO_InitStruct;
  if(adcHandle->Instance==ADC1)
  {
#endif
  /* USER CODE END ADC1_MspInit 0 */
    /* ADC1 clock enable */
    HAL_RCC_ADC_CLK_ENABLED++;
    if(HAL_RCC_ADC_CLK_ENABLED==1){
      __HAL_RCC_ADC_CLK_ENABLE();
    }
  
    /**ADC1 GPIO Configuration    
    PA3     ------> ADC1_IN8 
    */
    GPIO_InitStruct.Pin = MCU_VSOL_ADC1_Pin;
    GPIO_InitStruct.Mode = GPIO_MODE_ANALOG_ADC_CONTROL;
    GPIO_InitStruct.Pull = GPIO_NOPULL;
    HAL_GPIO_Init(MCU_VSOL_ADC1_GPIO_Port, &GPIO_InitStruct);

    /* ADC1 DMA Init */
    /* ADC1 Init */
    hdma_adc1.Instance = DMA1_Channel1;
    hdma_adc1.Init.Request = DMA_REQUEST_0;
    hdma_adc1.Init.Direction = DMA_PERIPH_TO_MEMORY;
    hdma_adc1.Init.PeriphInc = DMA_PINC_DISABLE;
    hdma_adc1.Init.MemInc = DMA_MINC_ENABLE;
    hdma_adc1.Init.PeriphDataAlignment = DMA_PDATAALIGN_HALFWORD;
    hdma_adc1.Init.MemDataAlignment = DMA_MDATAALIGN_HALFWORD;
    hdma_adc1.Init.Mode = DMA_NORMAL;
    hdma_adc1.Init.Priority = DMA_PRIORITY_LOW;
    if (HAL_DMA_Init(&hdma_adc1) != HAL_OK)
    {
      _Error_Handler(__FILE__, __LINE__);
    }

    __HAL_LINKDMA(adcHandle,DMA_Handle,hdma_adc1);

    /* ADC1 interrupt Init */
    HAL_NVIC_SetPriority(ADC1_2_IRQn, 5, 0);
    HAL_NVIC_EnableIRQ(ADC1_2_IRQn);
  }
  else if(adcHandle->Instance==ADC3)
  {
    /* ADC3 clock enable */
    HAL_RCC_ADC_CLK_ENABLED++;
    if(HAL_RCC_ADC_CLK_ENABLED==1){
      __HAL_RCC_ADC_CLK_ENABLE();
    }
  
    /**ADC3 GPIO Configuration    
    PF3     ------> ADC3_IN6 
    */
    GPIO_InitStruct.Pin = ADC3_IN6_20MHZ_PULL_Pin;
    GPIO_InitStruct.Mode = GPIO_MODE_ANALOG_ADC_CONTROL;
    GPIO_InitStruct.Pull = GPIO_NOPULL;
    HAL_GPIO_Init(ADC3_IN6_20MHZ_PULL_GPIO_Port, &GPIO_InitStruct);

    /* ADC3 DMA Init */
    /* ADC3 Init */
    hdma_adc3.Instance = DMA1_Channel3;
    hdma_adc3.Init.Request = DMA_REQUEST_0;
    hdma_adc3.Init.Direction = DMA_PERIPH_TO_MEMORY;
    hdma_adc3.Init.PeriphInc = DMA_PINC_DISABLE;
    hdma_adc3.Init.MemInc = DMA_MINC_ENABLE;
    hdma_adc3.Init.PeriphDataAlignment = DMA_PDATAALIGN_HALFWORD;
    hdma_adc3.Init.MemDataAlignment = DMA_MDATAALIGN_HALFWORD;
    hdma_adc3.Init.Mode = DMA_NORMAL;
    hdma_adc3.Init.Priority = DMA_PRIORITY_LOW;
    if (HAL_DMA_Init(&hdma_adc3) != HAL_OK)
    {
      _Error_Handler(__FILE__, __LINE__);
    }

    __HAL_LINKDMA(adcHandle,DMA_Handle,hdma_adc3);

    /* ADC3 interrupt Init */
    HAL_NVIC_SetPriority(ADC3_IRQn, 5, 0);
    HAL_NVIC_EnableIRQ(ADC3_IRQn);
  }
}

void HAL_ADC_MspDeInit(ADC_HandleTypeDef* adcHandle)
{

  if(adcHandle->Instance==ADC1)
  {
    /* Peripheral clock disable */
    HAL_RCC_ADC_CLK_ENABLED--;
    if(HAL_RCC_ADC_CLK_ENABLED==0){
      __HAL_RCC_ADC_CLK_DISABLE();
    }
  
    /**ADC1 GPIO Configuration    
    PA3     ------> ADC1_IN8 
    */
    HAL_GPIO_DeInit(MCU_VSOL_ADC1_GPIO_Port, MCU_VSOL_ADC1_Pin);

    /* ADC1 DMA DeInit */
    HAL_DMA_DeInit(adcHandle->DMA_Handle);

    /* ADC1 interrupt Deinit */
    HAL_NVIC_DisableIRQ(ADC1_2_IRQn);
  }
  else if(adcHandle->Instance==ADC3)
  {
    /* Peripheral clock disable */
    HAL_RCC_ADC_CLK_ENABLED--;
    if(HAL_RCC_ADC_CLK_ENABLED==0){
      __HAL_RCC_ADC_CLK_DISABLE();
    }
  
    /**ADC3 GPIO Configuration    
    PF3     ------> ADC3_IN6 
    */
    HAL_GPIO_DeInit(ADC3_IN6_20MHZ_PULL_GPIO_Port, ADC3_IN6_20MHZ_PULL_Pin);

    /* ADC3 DMA DeInit */
    HAL_DMA_DeInit(adcHandle->DMA_Handle);

    /* ADC3 interrupt Deinit */
    HAL_NVIC_DisableIRQ(ADC3_IRQn);
  }
} 

/**
  * @}
  */

/**
  * @}
  */

/************************ (C) COPYRIGHT STMicroelectronics *****END OF FILE****/
