DF4IAH/HFT-Core-Module/SW/HFT-Core-Module_TrueSTUDIO/Core/Src/i2c.c

/**
  ******************************************************************************
  * File Name          : I2C.c
  * Description        : This file provides code for the configuration
  *                      of the I2C instances.
  ******************************************************************************
  * This notice applies to any and all portions of this file
  * that are not between comment pairs USER CODE BEGIN and
  * USER CODE END. Other portions of this file, whether 
  * inserted by the user or by software development tools
  * are owned by their respective copyright owners.
  *
  * Copyright (c) 2018 STMicroelectronics International N.V. 
  * All rights reserved.
  *
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
  ******************************************************************************
  */

/* Includes ------------------------------------------------------------------*/
#include "i2c.h"

#include "gpio.h"

/* USER CODE BEGIN 0 */
#ifdef STD_INIT
/* USER CODE END 0 */

I2C_HandleTypeDef hi2c1;
I2C_HandleTypeDef hi2c2;
I2C_HandleTypeDef hi2c3;
I2C_HandleTypeDef hi2c4;

/* I2C1 init function */
void MX_I2C1_Init(void)
{

  hi2c1.Instance = I2C1;
  hi2c1.Init.Timing = 0x00000000;
  hi2c1.Init.OwnAddress1 = 0;
  hi2c1.Init.AddressingMode = I2C_ADDRESSINGMODE_7BIT;
  hi2c1.Init.DualAddressMode = I2C_DUALADDRESS_DISABLE;
  hi2c1.Init.OwnAddress2 = 0;
  hi2c1.Init.OwnAddress2Masks = I2C_OA2_NOMASK;
  hi2c1.Init.GeneralCallMode = I2C_GENERALCALL_DISABLE;
  hi2c1.Init.NoStretchMode = I2C_NOSTRETCH_DISABLE;
  if (HAL_I2C_Init(&hi2c1) != HAL_OK)
  {
    _Error_Handler(__FILE__, __LINE__);
  }

    /**Configure Analogue filter 
    */
  if (HAL_I2CEx_ConfigAnalogFilter(&hi2c1, I2C_ANALOGFILTER_ENABLE) != HAL_OK)
  {
    _Error_Handler(__FILE__, __LINE__);
  }

    /**Configure Digital filter 
    */
  if (HAL_I2CEx_ConfigDigitalFilter(&hi2c1, 3) != HAL_OK)
  {
    _Error_Handler(__FILE__, __LINE__);
  }

}
/* I2C2 init function */
void MX_I2C2_Init(void)
{

  hi2c2.Instance = I2C2;
  hi2c2.Init.Timing = 0x00000000;
  hi2c2.Init.OwnAddress1 = 0;
  hi2c2.Init.AddressingMode = I2C_ADDRESSINGMODE_7BIT;
  hi2c2.Init.DualAddressMode = I2C_DUALADDRESS_DISABLE;
  hi2c2.Init.OwnAddress2 = 0;
  hi2c2.Init.OwnAddress2Masks = I2C_OA2_NOMASK;
  hi2c2.Init.GeneralCallMode = I2C_GENERALCALL_DISABLE;
  hi2c2.Init.NoStretchMode = I2C_NOSTRETCH_DISABLE;
  if (HAL_I2C_Init(&hi2c2) != HAL_OK)
  {
    _Error_Handler(__FILE__, __LINE__);
  }

    /**Configure Analogue filter 
    */
  if (HAL_I2CEx_ConfigAnalogFilter(&hi2c2, I2C_ANALOGFILTER_ENABLE) != HAL_OK)
  {
    _Error_Handler(__FILE__, __LINE__);
  }

    /**Configure Digital filter 
    */
  if (HAL_I2CEx_ConfigDigitalFilter(&hi2c2, 3) != HAL_OK)
  {
    _Error_Handler(__FILE__, __LINE__);
  }

}
/* I2C3 init function */
void MX_I2C3_Init(void)
{

  hi2c3.Instance = I2C3;
  hi2c3.Init.Timing = 0x00000000;
  hi2c3.Init.OwnAddress1 = 0;
  hi2c3.Init.AddressingMode = I2C_ADDRESSINGMODE_7BIT;
  hi2c3.Init.DualAddressMode = I2C_DUALADDRESS_DISABLE;
  hi2c3.Init.OwnAddress2 = 0;
  hi2c3.Init.OwnAddress2Masks = I2C_OA2_NOMASK;
  hi2c3.Init.GeneralCallMode = I2C_GENERALCALL_DISABLE;
  hi2c3.Init.NoStretchMode = I2C_NOSTRETCH_DISABLE;
  if (HAL_I2C_Init(&hi2c3) != HAL_OK)
  {
    _Error_Handler(__FILE__, __LINE__);
  }

    /**Configure Analogue filter 
    */
  if (HAL_I2CEx_ConfigAnalogFilter(&hi2c3, I2C_ANALOGFILTER_ENABLE) != HAL_OK)
  {
    _Error_Handler(__FILE__, __LINE__);
  }

    /**Configure Digital filter 
    */
  if (HAL_I2CEx_ConfigDigitalFilter(&hi2c3, 3) != HAL_OK)
  {
    _Error_Handler(__FILE__, __LINE__);
  }

}
/* I2C4 init function */
void MX_I2C4_Init(void)
{

  hi2c4.Instance = I2C4;
  hi2c4.Init.Timing = 0x00000000;
  hi2c4.Init.OwnAddress1 = 0;
  hi2c4.Init.AddressingMode = I2C_ADDRESSINGMODE_7BIT;
  hi2c4.Init.DualAddressMode = I2C_DUALADDRESS_DISABLE;
  hi2c4.Init.OwnAddress2 = 0;
  hi2c4.Init.OwnAddress2Masks = I2C_OA2_NOMASK;
  hi2c4.Init.GeneralCallMode = I2C_GENERALCALL_DISABLE;
  hi2c4.Init.NoStretchMode = I2C_NOSTRETCH_DISABLE;
  if (HAL_I2C_Init(&hi2c4) != HAL_OK)
  {
    _Error_Handler(__FILE__, __LINE__);
  }

    /**Configure Analogue filter 
    */
  if (HAL_I2CEx_ConfigAnalogFilter(&hi2c4, I2C_ANALOGFILTER_ENABLE) != HAL_OK)
  {
    _Error_Handler(__FILE__, __LINE__);
  }

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
  {
    _Error_Handler(__FILE__, __LINE__);
  }

    /**Configure Digital filter
    */
  if (HAL_I2CEx_ConfigDigitalFilter(&hi2c4, 3) != HAL_OK)
  {
    _Error_Handler(__FILE__, __LINE__);
  }
}
#endif

void HAL_I2C_MspInit(I2C_HandleTypeDef* i2cHandle)
{

  GPIO_InitTypeDef GPIO_InitStruct;
  if(i2cHandle->Instance==I2C1)
  {
  /* USER CODE END I2C1_MspInit 0 */
  
    /**I2C1 GPIO Configuration    
    PG13     ------> I2C1_SDA
    PG14     ------> I2C1_SCL 
    */
    GPIO_InitStruct.Pin = MCU_I2C1_SDA_Pin;
    GPIO_InitStruct.Mode = GPIO_MODE_AF_OD;
    GPIO_InitStruct.Pull = GPIO_PULLUP;
    GPIO_InitStruct.Speed = GPIO_SPEED_FREQ_LOW;
    GPIO_InitStruct.Alternate = GPIO_AF4_I2C1;
    HAL_GPIO_Init(MCU_I2C1_SDA_GPIO_Port, &GPIO_InitStruct);

    GPIO_InitStruct.Pin = MCU_I2C1_SCL_Pin;
    GPIO_InitStruct.Mode = GPIO_MODE_AF_OD;
    GPIO_InitStruct.Pull = GPIO_NOPULL;
    GPIO_InitStruct.Speed = GPIO_SPEED_FREQ_LOW;
    GPIO_InitStruct.Alternate = GPIO_AF4_I2C1;
    HAL_GPIO_Init(MCU_I2C1_SCL_GPIO_Port, &GPIO_InitStruct);

    /* I2C1 clock enable */
    __HAL_RCC_I2C1_CLK_ENABLE();

    /* I2C1 interrupt Init */
    HAL_NVIC_SetPriority(I2C1_EV_IRQn, 5, 0);
    HAL_NVIC_EnableIRQ(I2C1_EV_IRQn);
    HAL_NVIC_SetPriority(I2C1_ER_IRQn, 5, 0);
    HAL_NVIC_EnableIRQ(I2C1_ER_IRQn);
  }
  else if(i2cHandle->Instance==I2C2)
  {
  
    /**I2C2 GPIO Configuration    
    PF0     ------> I2C2_SDA
    PF1     ------> I2C2_SCL 
    */
    GPIO_InitStruct.Pin = MCU_I2C2_SDA_Pin;
    GPIO_InitStruct.Mode = GPIO_MODE_AF_OD;
    GPIO_InitStruct.Pull = GPIO_PULLUP;
    GPIO_InitStruct.Speed = GPIO_SPEED_FREQ_LOW;
    GPIO_InitStruct.Alternate = GPIO_AF4_I2C2;
    HAL_GPIO_Init(MCU_I2C2_SDA_GPIO_Port, &GPIO_InitStruct);

    GPIO_InitStruct.Pin = MCU_I2C2_SCL_Pin;
    GPIO_InitStruct.Mode = GPIO_MODE_AF_OD;
    GPIO_InitStruct.Pull = GPIO_NOPULL;
    GPIO_InitStruct.Speed = GPIO_SPEED_FREQ_LOW;
    GPIO_InitStruct.Alternate = GPIO_AF4_I2C2;
    HAL_GPIO_Init(MCU_I2C2_SCL_GPIO_Port, &GPIO_InitStruct);

    /* I2C2 clock enable */
    __HAL_RCC_I2C2_CLK_ENABLE();

    /* I2C2 interrupt Init */
    HAL_NVIC_SetPriority(I2C2_EV_IRQn, 5, 0);
    HAL_NVIC_EnableIRQ(I2C2_EV_IRQn);
    HAL_NVIC_SetPriority(I2C2_ER_IRQn, 5, 0);
    HAL_NVIC_EnableIRQ(I2C2_ER_IRQn);
  }
  else if(i2cHandle->Instance==I2C3)
  {
  
    /**I2C3 GPIO Configuration    
    PG7     ------> I2C3_SCL
    PG8     ------> I2C3_SDA 
    */
    GPIO_InitStruct.Pin = MCU_I2C3_SCL_Pin;
    GPIO_InitStruct.Mode = GPIO_MODE_AF_OD;
    GPIO_InitStruct.Pull = GPIO_NOPULL;
    GPIO_InitStruct.Speed = GPIO_SPEED_FREQ_LOW;
    GPIO_InitStruct.Alternate = GPIO_AF4_I2C3;
    HAL_GPIO_Init(MCU_I2C3_SCL_GPIO_Port, &GPIO_InitStruct);

    GPIO_InitStruct.Pin = MCU_I2C3_SDA_Pin;
    GPIO_InitStruct.Mode = GPIO_MODE_AF_OD;
    GPIO_InitStruct.Pull = GPIO_PULLUP;
    GPIO_InitStruct.Speed = GPIO_SPEED_FREQ_LOW;
    GPIO_InitStruct.Alternate = GPIO_AF4_I2C3;
    HAL_GPIO_Init(MCU_I2C3_SDA_GPIO_Port, &GPIO_InitStruct);

    /* I2C3 clock enable */
    __HAL_RCC_I2C3_CLK_ENABLE();

    /* I2C3 interrupt Init */
    HAL_NVIC_SetPriority(I2C3_EV_IRQn, 5, 0);
    HAL_NVIC_EnableIRQ(I2C3_EV_IRQn);
    HAL_NVIC_SetPriority(I2C3_ER_IRQn, 5, 0);
    HAL_NVIC_EnableIRQ(I2C3_ER_IRQn);
  }
  else if(i2cHandle->Instance==I2C4)
  {
  
    /**I2C4 GPIO Configuration    
    PF14     ------> I2C4_SCL
    PD13     ------> I2C4_SDA 
    */
    GPIO_InitStruct.Pin = MCU_I2C4_SCL_Pin;
    GPIO_InitStruct.Mode = GPIO_MODE_AF_OD;
    GPIO_InitStruct.Pull = GPIO_NOPULL;
    GPIO_InitStruct.Speed = GPIO_SPEED_FREQ_LOW;
    GPIO_InitStruct.Alternate = GPIO_AF4_I2C4;
    HAL_GPIO_Init(MCU_I2C4_SCL_GPIO_Port, &GPIO_InitStruct);

    GPIO_InitStruct.Pin = MCU_I2C4_SDA_Pin;
    GPIO_InitStruct.Mode = GPIO_MODE_AF_OD;
    GPIO_InitStruct.Pull = GPIO_PULLUP;
    GPIO_InitStruct.Speed = GPIO_SPEED_FREQ_LOW;
    GPIO_InitStruct.Alternate = GPIO_AF4_I2C4;
    HAL_GPIO_Init(MCU_I2C4_SDA_GPIO_Port, &GPIO_InitStruct);

    /* I2C4 clock enable */
    __HAL_RCC_I2C4_CLK_ENABLE();

    /* I2C4 interrupt Init */
    HAL_NVIC_SetPriority(I2C4_EV_IRQn, 5, 0);
    HAL_NVIC_EnableIRQ(I2C4_EV_IRQn);
    HAL_NVIC_SetPriority(I2C4_ER_IRQn, 5, 0);
    HAL_NVIC_EnableIRQ(I2C4_ER_IRQn);
  }
}

void HAL_I2C_MspDeInit(I2C_HandleTypeDef* i2cHandle)
{

  if(i2cHandle->Instance==I2C1)
  {
    /* Peripheral clock disable */
    __HAL_RCC_I2C1_CLK_DISABLE();
  
    /**I2C1 GPIO Configuration    
    PG13     ------> I2C1_SDA
    PG14     ------> I2C1_SCL 
    */
    HAL_GPIO_DeInit(GPIOG, MCU_I2C1_SDA_Pin|MCU_I2C1_SCL_Pin);

    /* I2C1 interrupt Deinit */
    HAL_NVIC_DisableIRQ(I2C1_EV_IRQn);
    HAL_NVIC_DisableIRQ(I2C1_ER_IRQn);
  }
  else if(i2cHandle->Instance==I2C2)
  {
    /* Peripheral clock disable */
    __HAL_RCC_I2C2_CLK_DISABLE();
  
    /**I2C2 GPIO Configuration    
    PF0     ------> I2C2_SDA
    PF1     ------> I2C2_SCL 
    */
    HAL_GPIO_DeInit(GPIOF, MCU_I2C2_SDA_Pin|MCU_I2C2_SCL_Pin);

    /* I2C2 interrupt Deinit */
    HAL_NVIC_DisableIRQ(I2C2_EV_IRQn);
    HAL_NVIC_DisableIRQ(I2C2_ER_IRQn);
  }
  else if(i2cHandle->Instance==I2C3)
  {
    /* Peripheral clock disable */
    __HAL_RCC_I2C3_CLK_DISABLE();
  
    /**I2C3 GPIO Configuration    
    PG7     ------> I2C3_SCL
    PG8     ------> I2C3_SDA 
    */
    HAL_GPIO_DeInit(GPIOG, MCU_I2C3_SCL_Pin|MCU_I2C3_SDA_Pin);

    /* I2C3 interrupt Deinit */
    HAL_NVIC_DisableIRQ(I2C3_EV_IRQn);
    HAL_NVIC_DisableIRQ(I2C3_ER_IRQn);
  }
  else if(i2cHandle->Instance==I2C4)
  {
    /* Peripheral clock disable */
    __HAL_RCC_I2C4_CLK_DISABLE();
  
    /**I2C4 GPIO Configuration    
    PF14     ------> I2C4_SCL
    PD13     ------> I2C4_SDA 
    */
    HAL_GPIO_DeInit(MCU_I2C4_SCL_GPIO_Port, MCU_I2C4_SCL_Pin);

    HAL_GPIO_DeInit(MCU_I2C4_SDA_GPIO_Port, MCU_I2C4_SDA_Pin);

    /* I2C4 interrupt Deinit */
    HAL_NVIC_DisableIRQ(I2C4_EV_IRQn);
    HAL_NVIC_DisableIRQ(I2C4_ER_IRQn);
  }
} 

/**
  * @}
  */

/**
  * @}
  */

/************************ (C) COPYRIGHT STMicroelectronics *****END OF FILE****/
