DF4IAH/HFT-Core-Module/SW/HFT-Core-Module_TrueSTUDIO/App/Inc/task_AX5243.h

/*
 * task_AX5243.h
 *
 *  Created on: 10.09.2018
 *      Author: DF4IAH
 */

#ifndef TASK_AX5243_H_
#define TASK_AX5243_H_

#include "stm32l4xx_hal.h"
#include "main.h"


#if 0
/* NEW CODE */

#if 0
# define USART_SPI_AX                                         USARTC1
#else
# define SPI_AX                                               SPIC
#endif

#ifndef IOPORT_MODE_FALLING
# define IOPORT_MODE_FALLING                                  0x02
#endif
#endif


#define C_PR1200_CALL_LENGTH                                  6

#define C_AX_PRW_LENGTH                                       253
#define C_SPI_AX_BUFFER_LENGTH                                512
#define C_SPI_AX_RANGE_NOT_SET                                0x10

#define C_AX_REG_RD                                           0x00U
#define C_AX_REG_WR                                           0x80U


typedef enum SPI_AX_TRPT_STATE_ENUM {

  SPI_AX_TRPT_STATE_DISABLED                                  = 0x00,
  SPI_AX_TRPT_STATE_ENA_ADDR,
  SPI_AX_TRPT_STATE_ENA_DATA_WRITE,
  SPI_AX_TRPT_STATE_ENA_DATA_READ,
  SPI_AX_TRPT_STATE_COMPLETE,

  SPI_AX_TRPT_STATE_END                                       = 0x7f,
  SPI_AX_TRPT_STATE_ERROR                                     = 0xff,

} SPI_AX_TRPT_STATE_t;
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
